Nolicx/Voron-Trident/Diagrams/Pins/SB2209 RP2040 Pinout.png

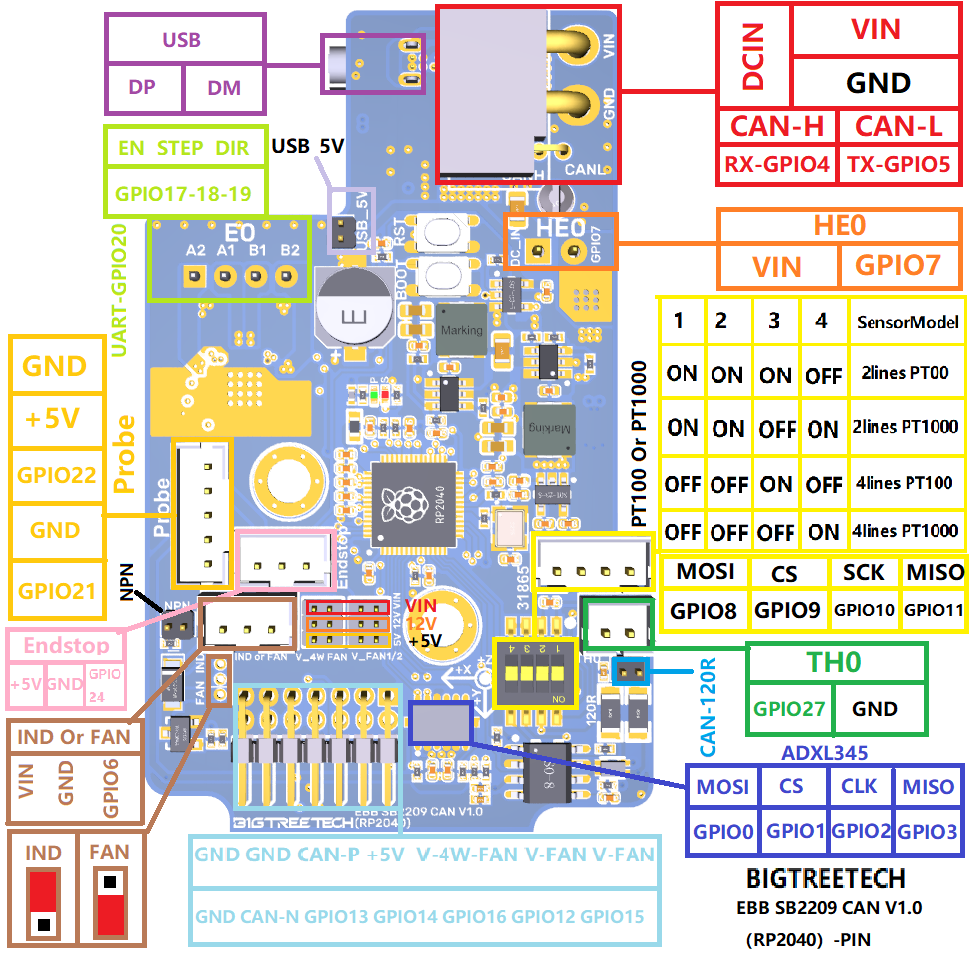
Diagrams/Pins/SB2209 RP2040 Pinout.png
