Nolicx/Voron-Trident/STL/ElectronicsBay/DIN_frame_mount_x4.stl

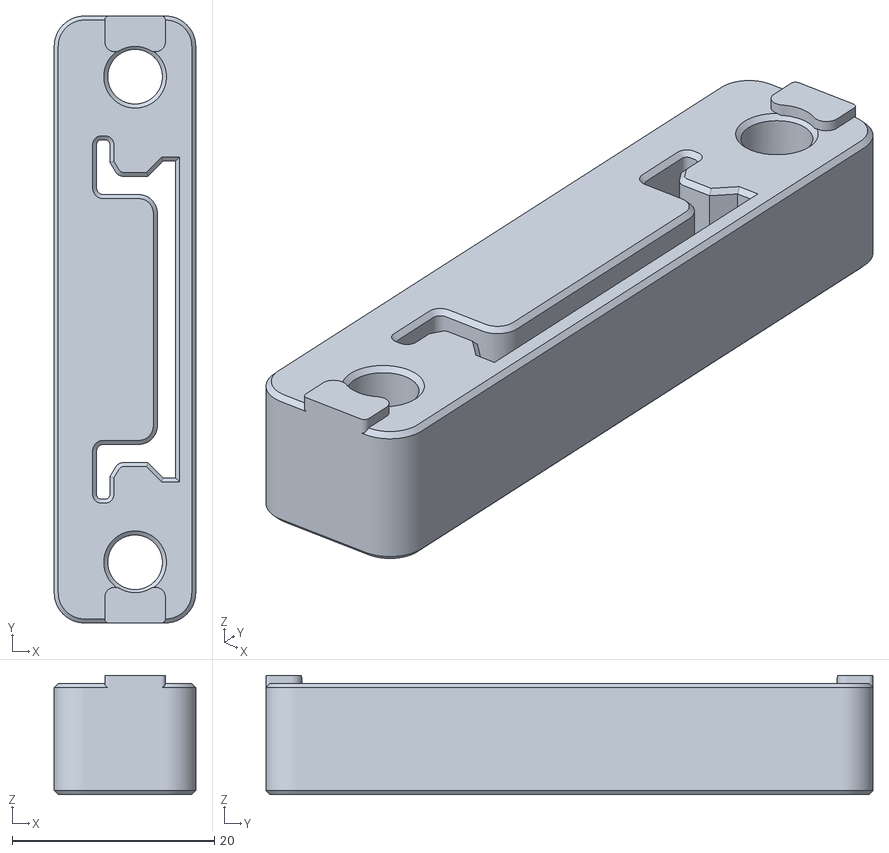
[picture p17: CAD file, 2025-08-13]
STL/ElectronicsBay/DIN_frame_mount_x4.stl
14.0 x 60.0 x 11.8
