Nolicx/Voron-Trident/STL/Exhaust_Filter/exhaust_filter_housing.stl

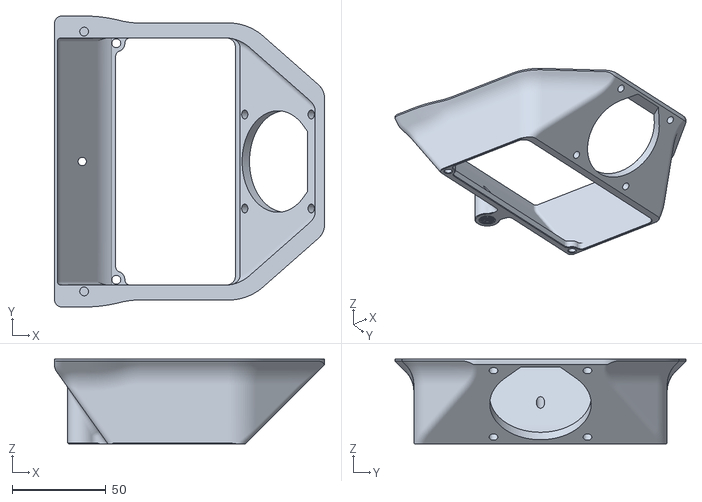
[picture p18: CAD file, 2025-08-13]
STL/Exhaust_Filter/exhaust_filter_housing.stl
143.7 x 154.8 x 45.0
