Nolicx/Voron-Trident/STL/Gantry/AB_Drive_Units/[a]_y_endstop_housing.stl

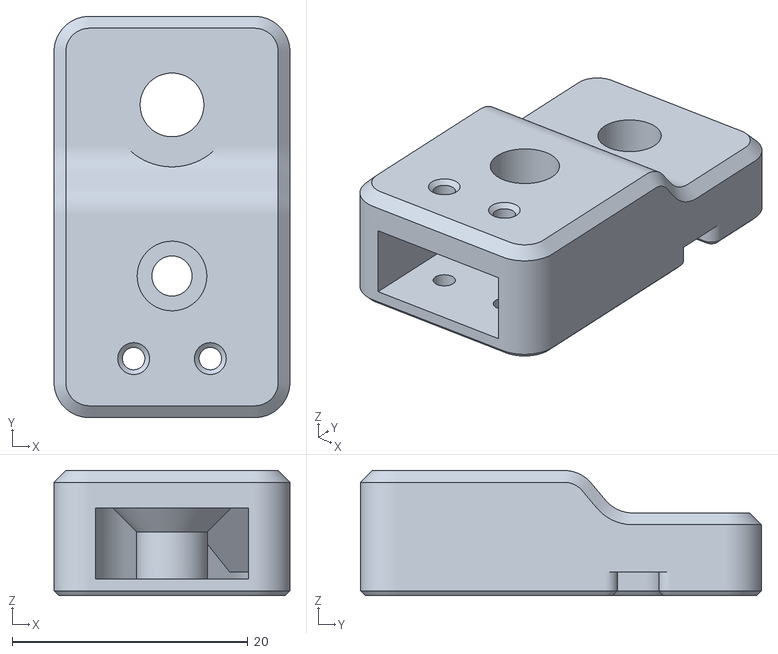
[picture p19: CAD file, 2025-08-13]
STL/Gantry/AB_Drive_Units/[a]_y_endstop_housing.stl
20.0 x 34.0 x 10.6
