Nolicx/Voron-Trident/STL/Gantry/PG7 Gantry Adapter.stl

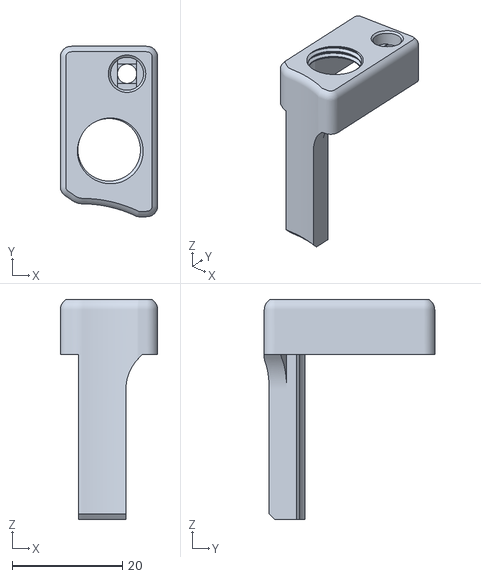
[picture p21: CAD file, 2025-08-13]
STL/Gantry/PG7 Gantry Adapter.stl
17.7 x 31.0 x 40.0
