Nolicx/Voron-Trident/STL/Gantry/XY_Joints/[a]_endstop_pod_hall_effect.stl

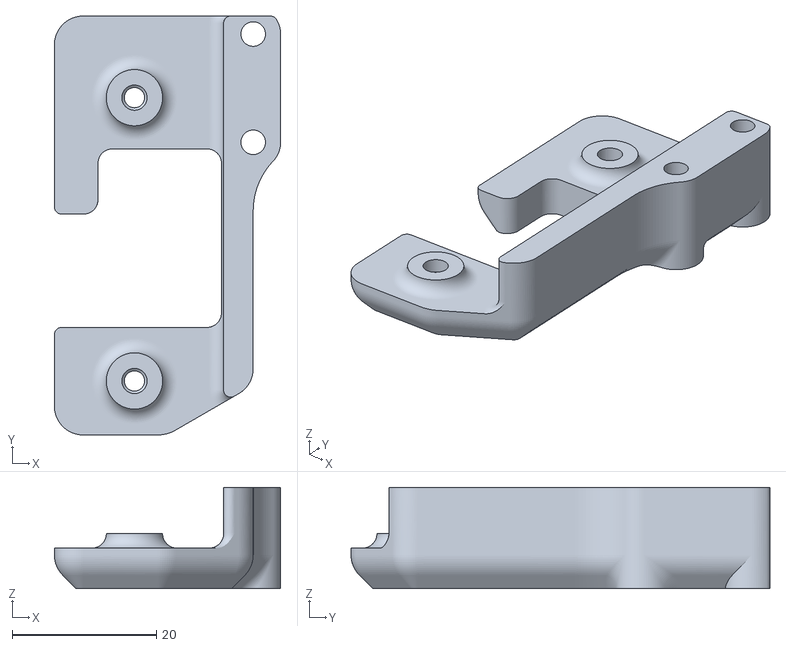
[picture p22: CAD file, 2025-08-13]
STL/Gantry/XY_Joints/[a]_endstop_pod_hall_effect.stl
31.4 x 58.0 x 14.0
