Nolicx/Voron-Trident/STL/Panels/bottom_panel_hinge_x2.stl

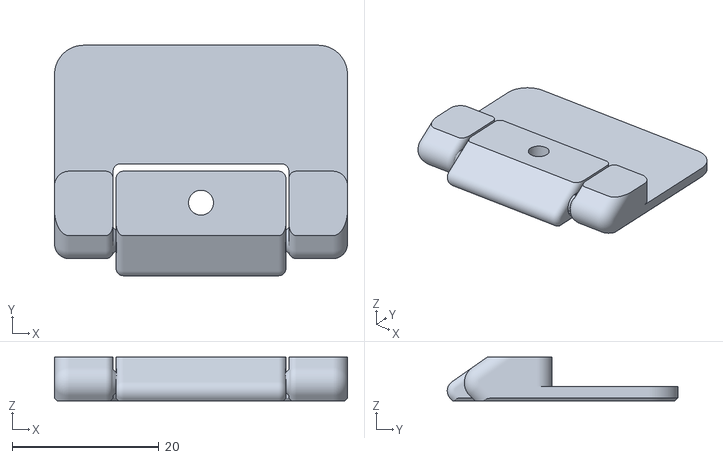
[picture p23: CAD file, 2025-08-13]
STL/Panels/bottom_panel_hinge_x2.stl
40.0 x 31.5 x 6.00
