Nolicx/Voron-Trident/STL/Panels/Front_Doors/handle_a_x2.stl

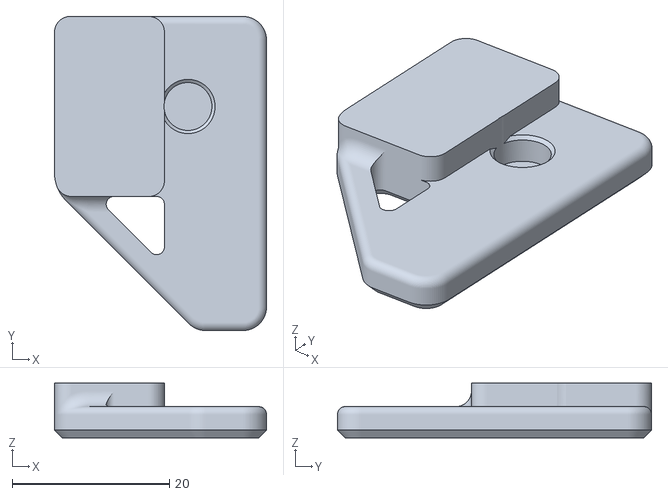
[picture p24: CAD file, 2025-08-13]
STL/Panels/Front_Doors/handle_a_x2.stl
27.0 x 40.0 x 7.00
