Nolicx/Voron-Trident/STL/Skirt/250/front_skirt_a_250.stl

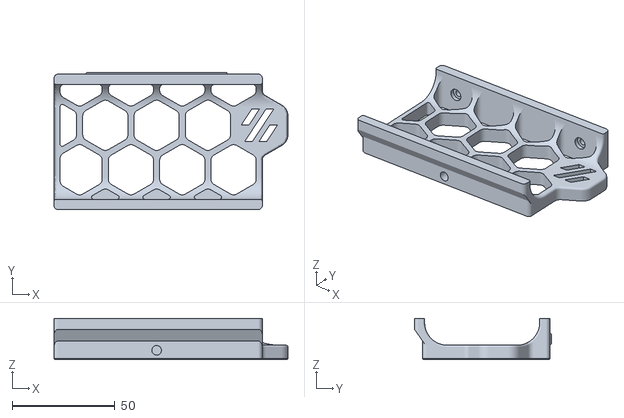
[picture p25: CAD file, 2025-08-13]
STL/Skirt/250/front_skirt_a_250.stl
114.0 x 66.8 x 20.0
