Nolicx/Voron-Trident/STL/Skirt/300/side_skirt_b_300_x2.stl

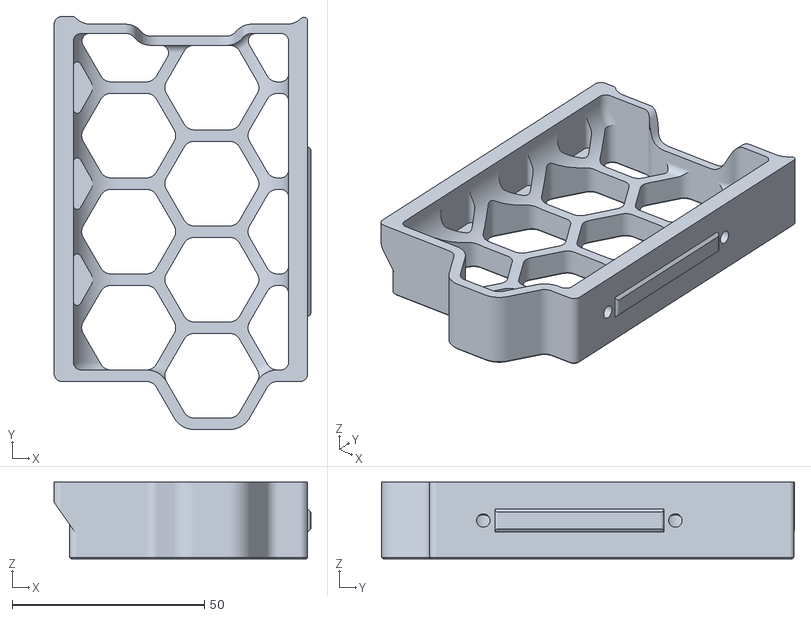
[picture p26: CAD file, 2025-08-13]
STL/Skirt/300/side_skirt_b_300_x2.stl
66.8 x 107.5 x 20.0
