Nolicx/Voron-Trident/STL/Skirt/350/front_skirt_a_350.stl

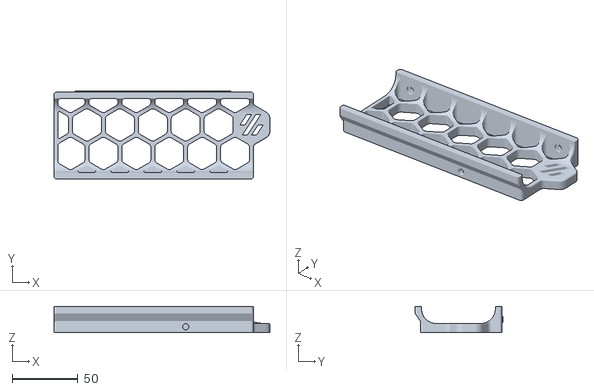
[picture p27: CAD file, 2025-08-13]
STL/Skirt/350/front_skirt_a_350.stl
164.0 x 66.8 x 20.0
