Nolicx/Voron-Trident/STL/Skirt/keystone_panel.stl

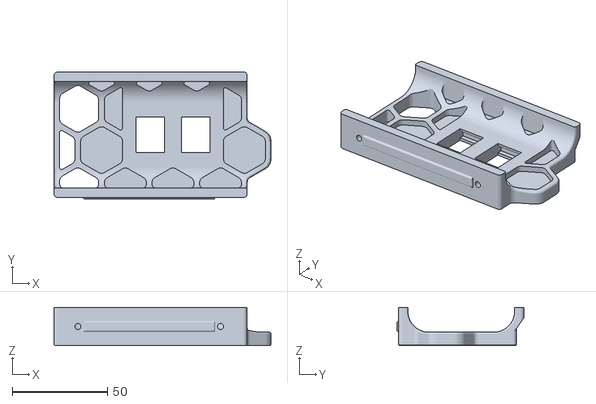
[picture p28: CAD file, 2025-08-13]
STL/Skirt/keystone_panel.stl
114.0 x 66.8 x 20.0
