Nolicx/Voron-Trident/STL/Spool_Management/bowden_retainer.stl

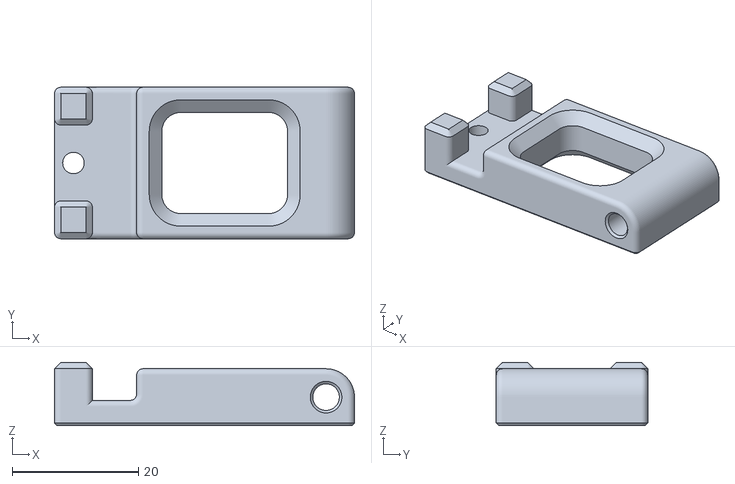
[picture p29: CAD file, 2025-08-13]
STL/Spool_Management/bowden_retainer.stl
47.5 x 24.0 x 10.00
