Nolicx/Voron-Trident/STL/Stealthburner/Clockwork2/[a]_anchor_pg7.stl

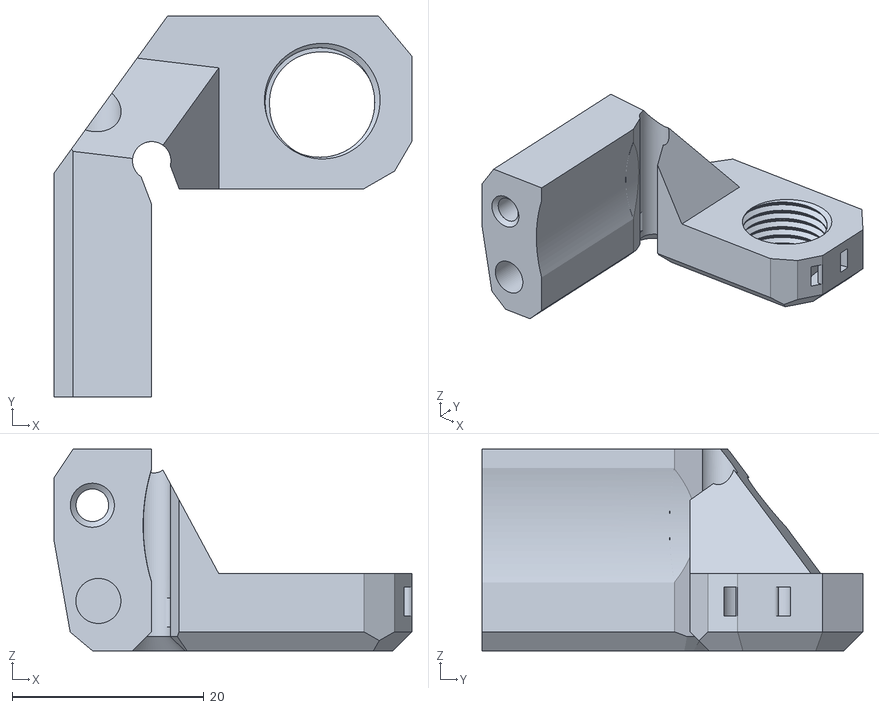
[picture p30: CAD file, 2025-08-13]
STL/Stealthburner/Clockwork2/[a]_anchor_pg7.stl
37.3 x 39.7 x 21.1
