Nolicx/Voron-Trident/STL/Stealthburner/Clockwork2/Direct_Drive/[a]_guidler_b.stl

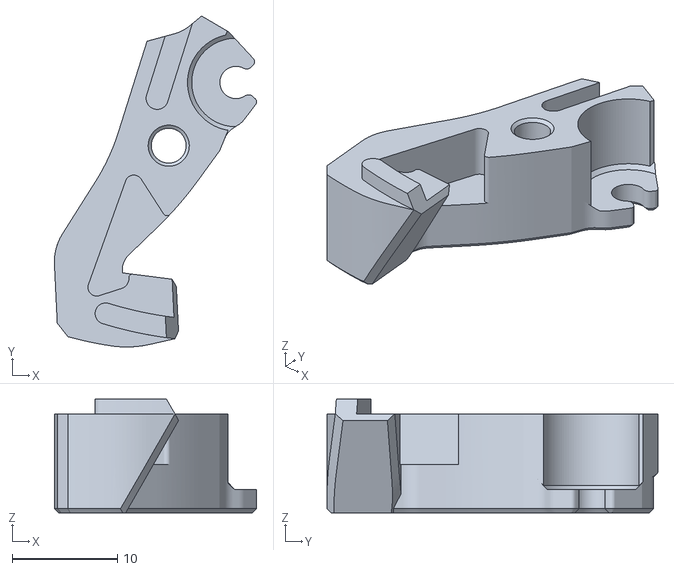
[picture p31: CAD file, 2025-08-13]
STL/Stealthburner/Clockwork2/Direct_Drive/[a]_guidler_b.stl
19.2 x 31.4 x 10.8
