Nolicx/Voron-Trident/STL/Stealthburner/Stealthburner/stealthburner_printhead_dragon_rear_cw2.stl

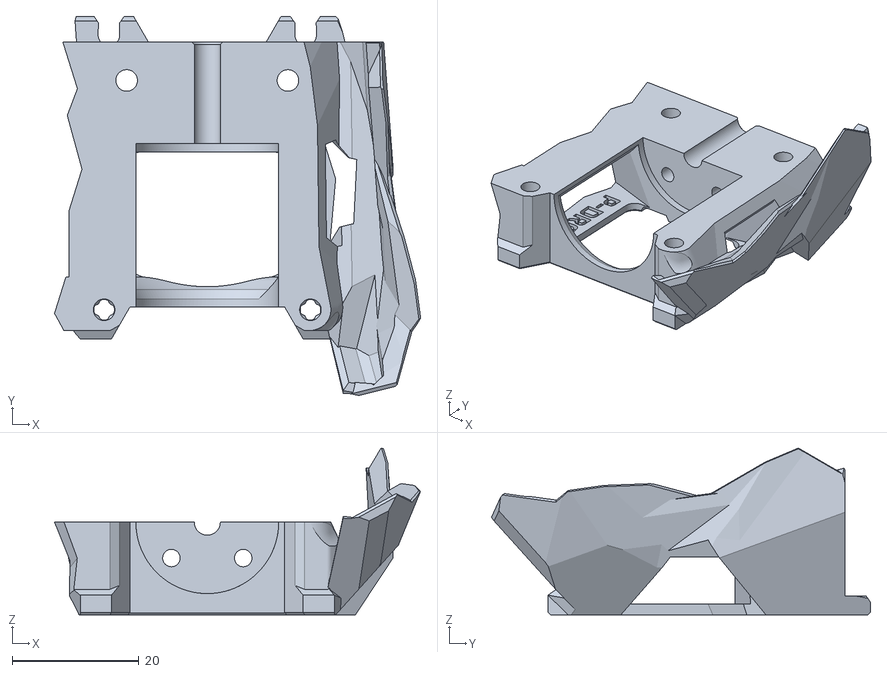
[picture p32: CAD file, 2025-08-13]
STL/Stealthburner/Stealthburner/stealthburner_printhead_dragon_rear_cw2.stl
57.7 x 59.7 x 26.3
