Nolicx/Voron-Trident/STL/Stealthburner/Tools/SB_5015_Cutting_Tool_B.stl

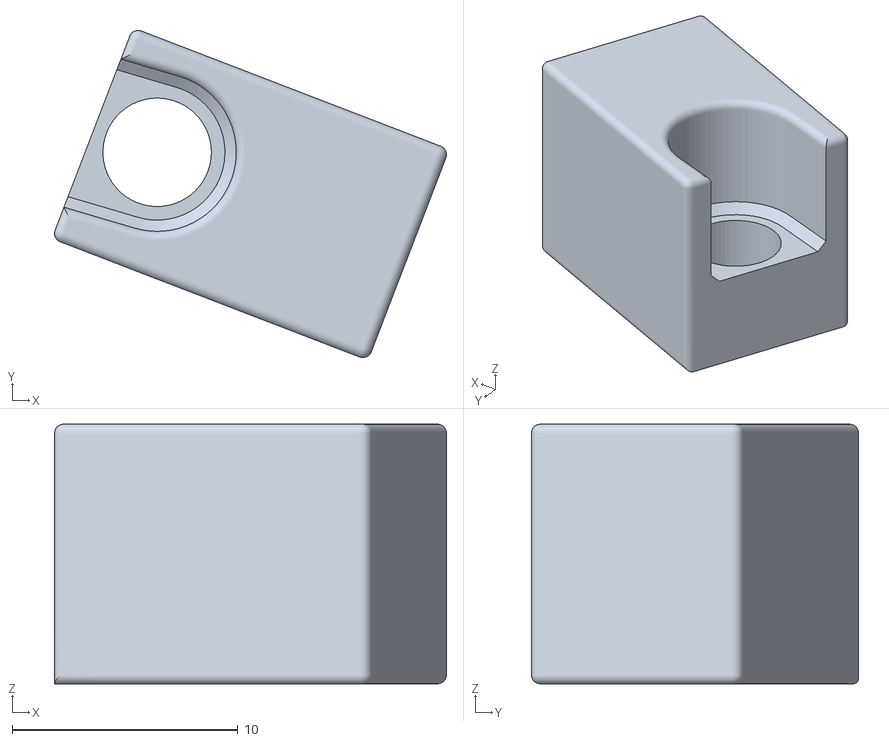
[picture p33: CAD file, 2025-08-13]
STL/Stealthburner/Tools/SB_5015_Cutting_Tool_B.stl
17.4 x 14.5 x 11.5
