Nolicx/Voron-Trident/STL/Tap/Tap_Upper_PCB_r8.stl

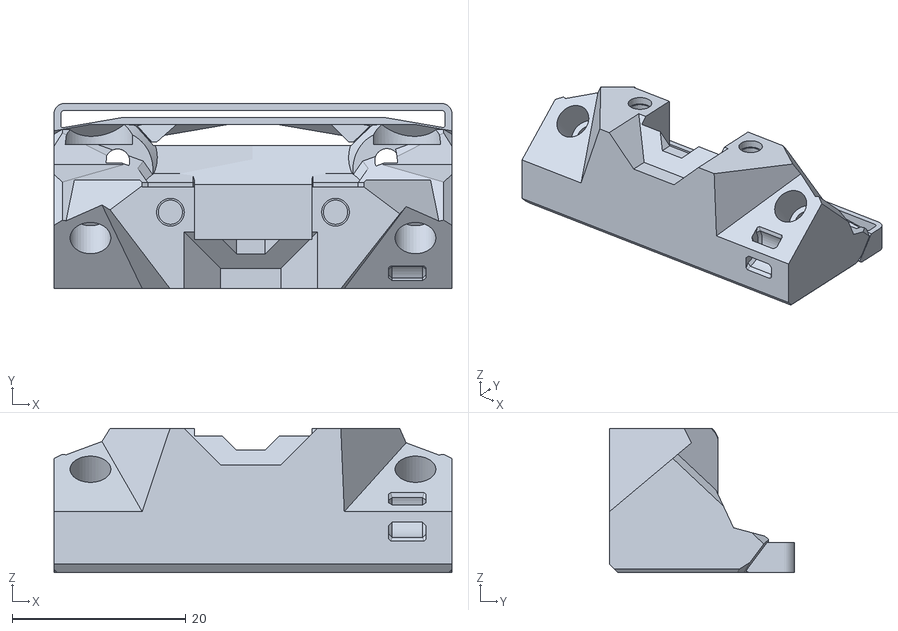
[picture p34: CAD file, 2025-08-13]
STL/Tap/Tap_Upper_PCB_r8.stl
45.8 x 21.3 x 16.6
