Nolicx/Voron-Trident/STL/Tools/pulley_jig.stl

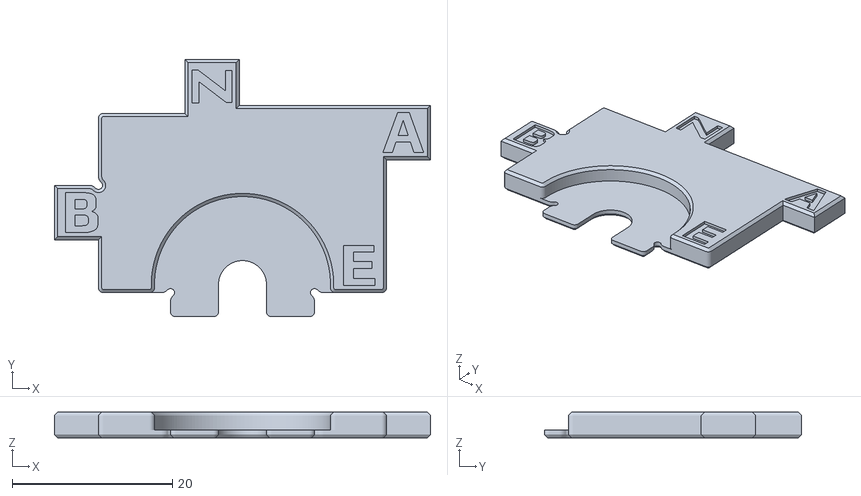
[picture p35: CAD file, 2025-08-13]
STL/Tools/pulley_jig.stl
47.0 x 32.2 x 3.20
