Nolicx/Voron-Trident/STL/Z_Assembly/z_rear_extrusionbracket_right.stl

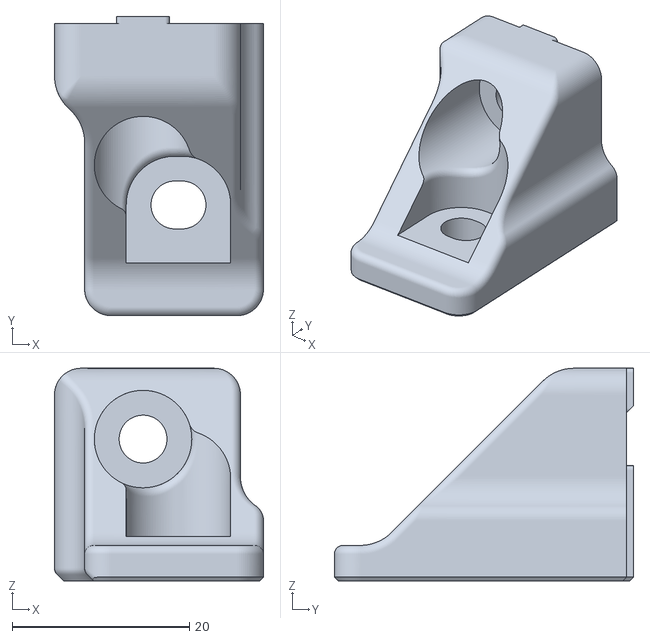
[picture p36: CAD file, 2025-08-13]
STL/Z_Assembly/z_rear_extrusionbracket_right.stl
23.6 x 33.8 x 24.0
