Nolicx/Voron-Trident/Mods/build_plate_stopper/Flex+Plate+Stops.stl

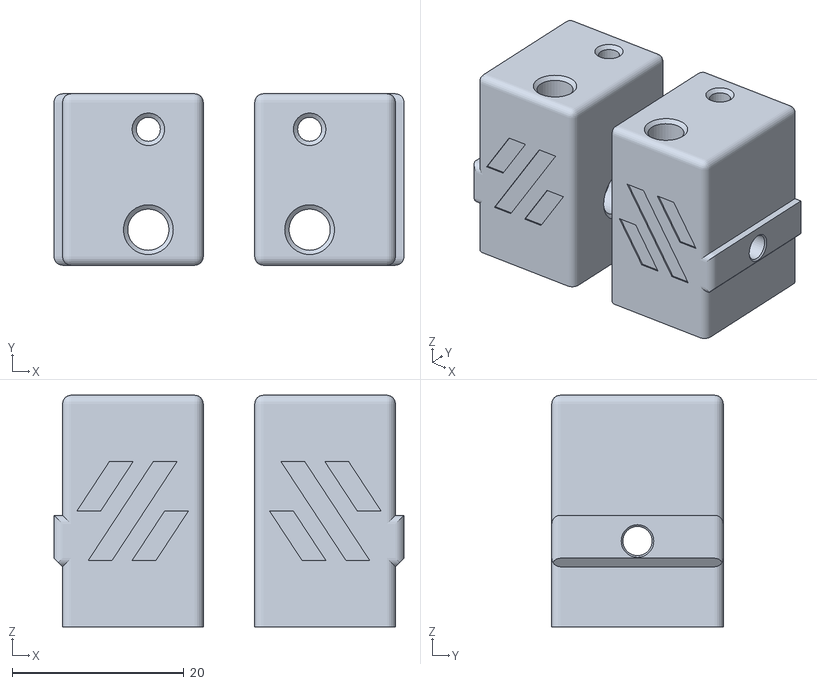
[picture p37: CAD file, 2026-03-26]
Mods/build_plate_stopper/Flex+Plate+Stops.stl
40.8 x 20.0 x 27.0
