Nolicx/Voron-Trident/Mods/spool_holders/Trident Internal Spool Holder rev2.0.stl

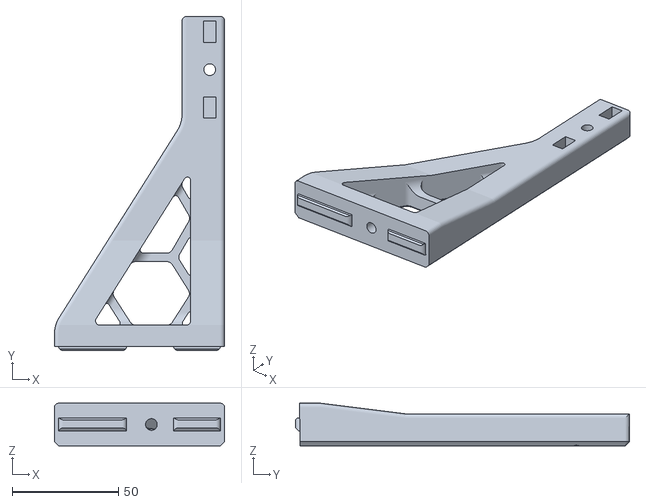
[picture p39: CAD file, 2026-03-26]
Mods/spool_holders/Trident Internal Spool Holder rev2.0.stl
80.0 x 156.9 x 20.0
