Nolicx/Voron-Trident/Mods/wago_mounts/Wago 221-413 3-Way Mount (x2).stl

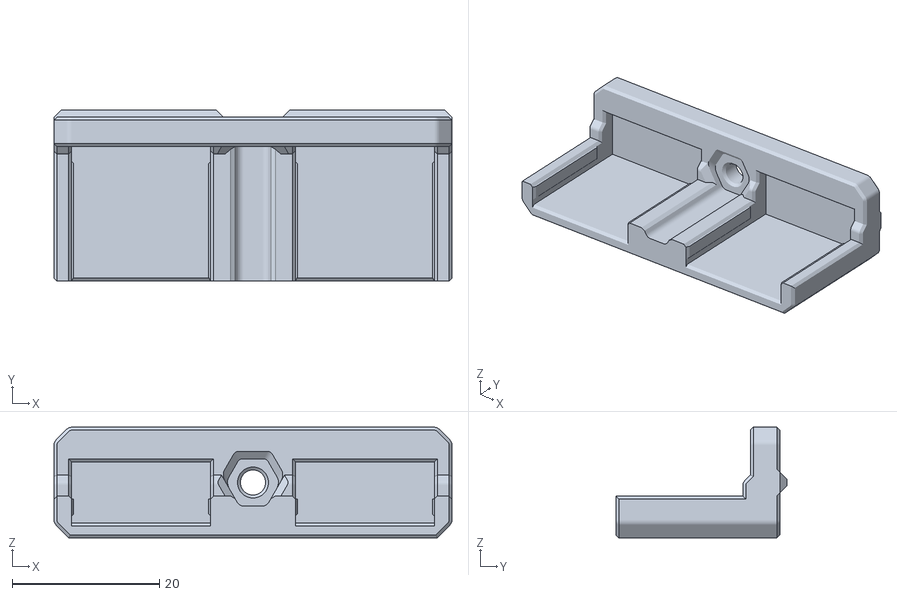
[picture p40: CAD file, 2026-05-21]
Mods/wago_mounts/Wago 221-413 3-Way Mount (x2).stl
54.0 x 23.2 x 15.0
