Nolicx/Voron-Trident/only custom STLs/Primary/cable support rod for CAN.STL

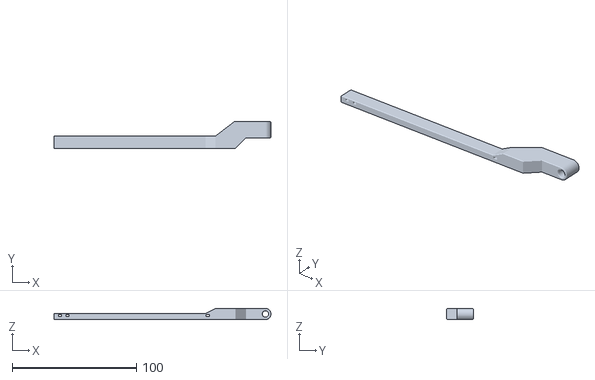
[picture p41: CAD file, 2025-08-13]
only custom STLs/Primary/cable support rod for CAN.STL
174.5 x 21.5 x 9.00
