Nolicx/Voron-Trident/only custom STLs/Primary/Nevermore/trident_bed_mount_bracket_right_r1.stl

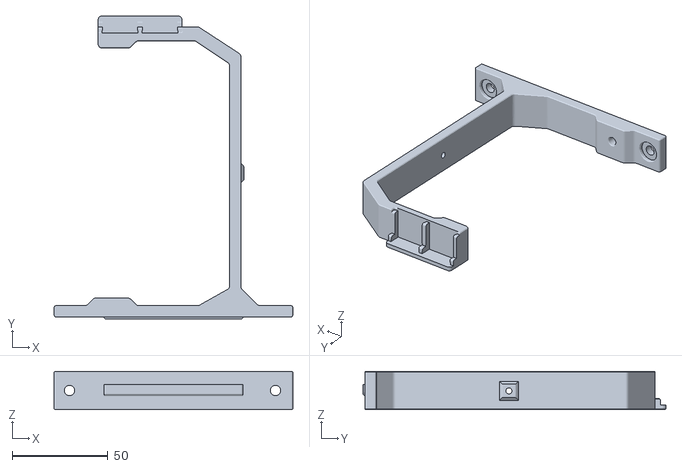
[picture p42: CAD file, 2025-08-13]
only custom STLs/Primary/Nevermore/trident_bed_mount_bracket_right_r1.stl
124.4 x 157.9 x 20.0
