Nolicx/Voron-Trident/STL/ElectronicsBay/lrs_psu_bracket_x2.stl

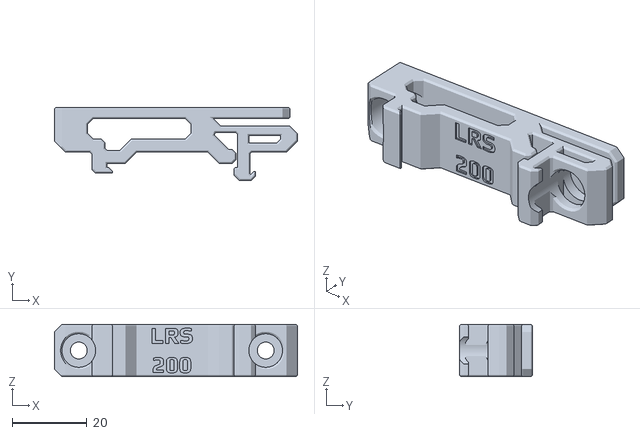
[picture p43: CAD file, 2025-08-13]
STL/ElectronicsBay/lrs_psu_bracket_x2.stl
65.0 x 19.6 x 14.0
