Nolicx/Voron-Trident/STL/Exhaust_Filter/exhaust_filter_grill.stl

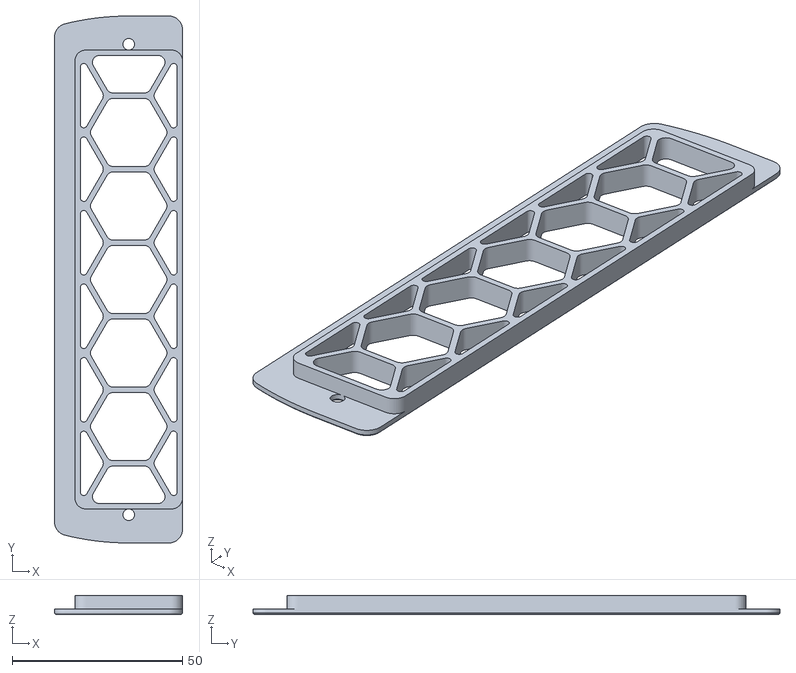
[picture p44: CAD file, 2025-08-13]
STL/Exhaust_Filter/exhaust_filter_grill.stl
37.6 x 154.8 x 5.60
