Nolicx/Voron-Trident/STL/Gantry/AB_Drive_Units/[a]_y_endstop_bumper.stl

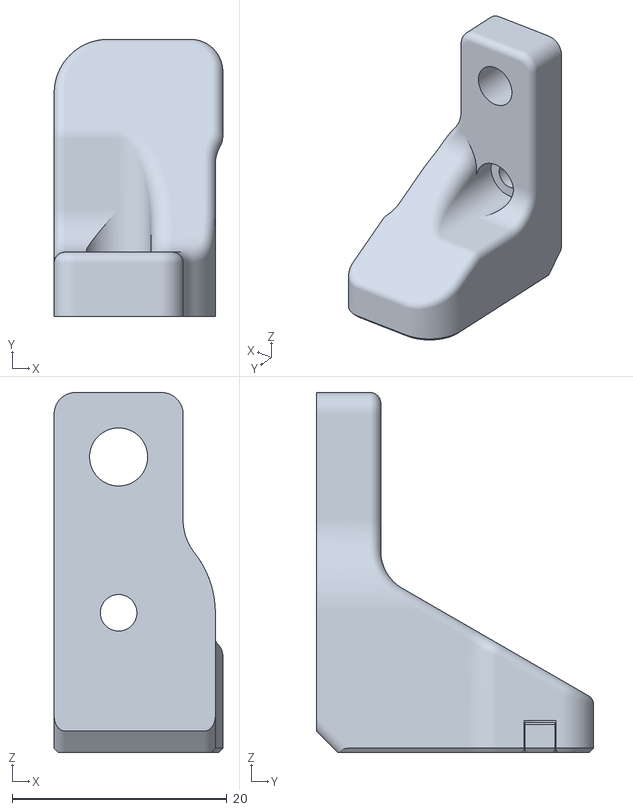
[picture p45: CAD file, 2025-08-13]
STL/Gantry/AB_Drive_Units/[a]_y_endstop_bumper.stl
15.7 x 25.8 x 33.5
