Nolicx/Voron-Trident/STL/Gantry/chain_wire_anchor_a_3hole.stl

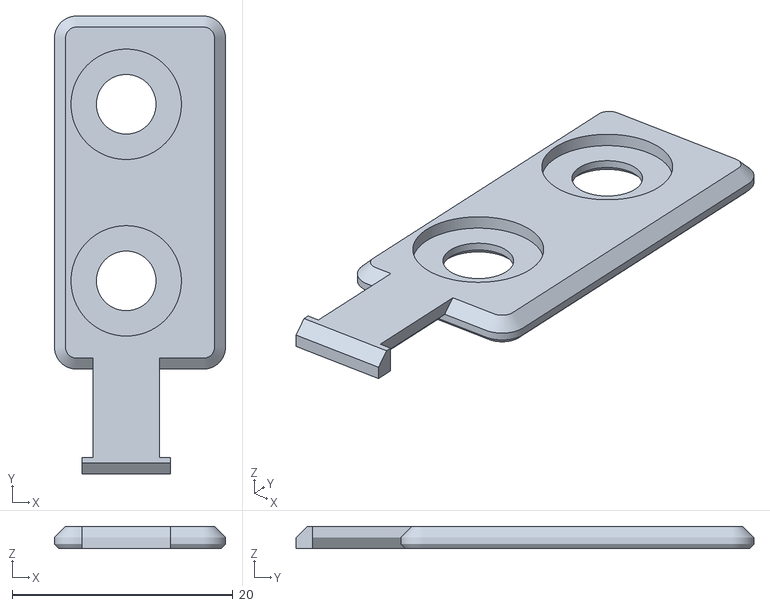
[picture p46: CAD file, 2025-08-13]
STL/Gantry/chain_wire_anchor_a_3hole.stl
15.5 x 41.5 x 2.00
