Nolicx/Voron-Trident/STL/Gantry/Front_Idlers/[a]_tensioner_left.stl

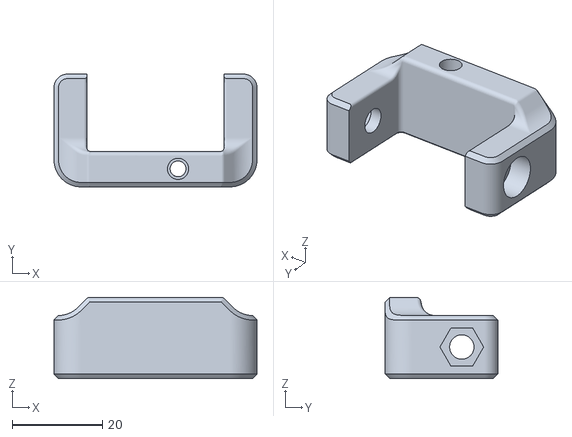
[picture p47: CAD file, 2025-08-13]
STL/Gantry/Front_Idlers/[a]_tensioner_left.stl
45.0 x 25.0 x 18.0
