Nolicx/Voron-Trident/STL/Gantry/XY_Joints/xy_joint_left_upper_MGN12.stl

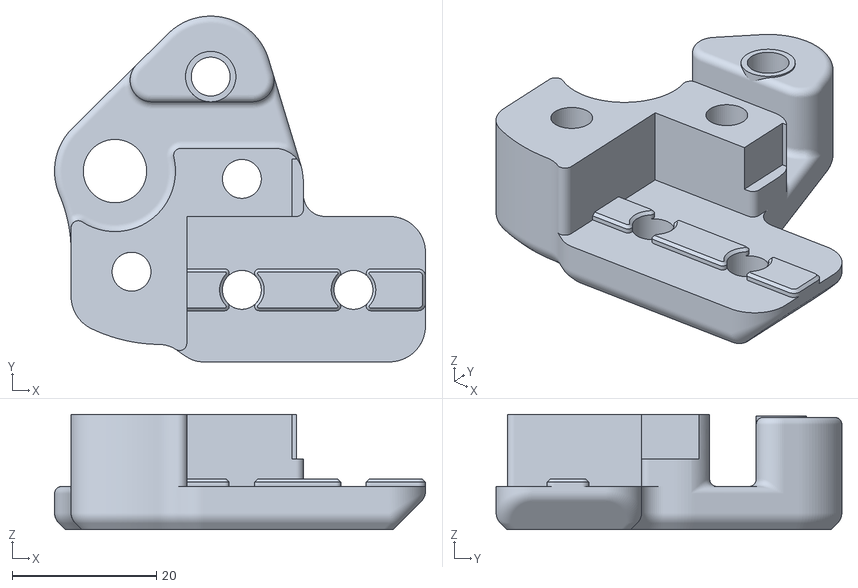
[picture p48: CAD file, 2025-08-13]
STL/Gantry/XY_Joints/xy_joint_left_upper_MGN12.stl
51.5 x 48.0 x 16.0
