Nolicx/Voron-Trident/STL/Nevermore/Trident_Bed_Mount_XL_Cartridge_LID.stl

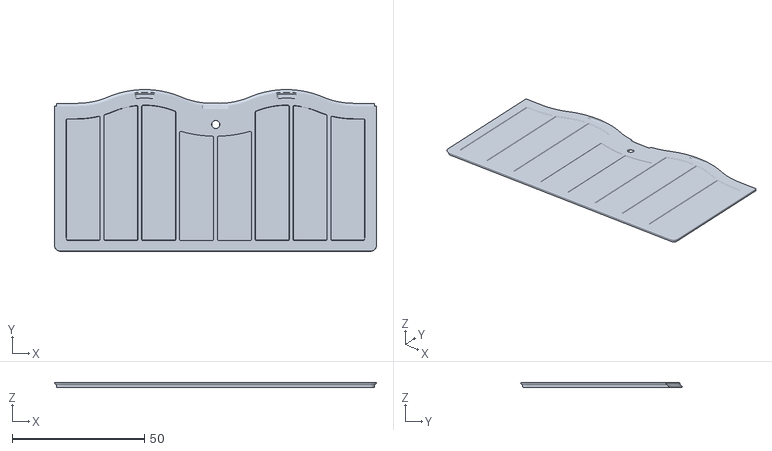
[picture p49: CAD file, 2025-08-13]
STL/Nevermore/Trident_Bed_Mount_XL_Cartridge_LID.stl
122.0 x 61.3 x 1.78
