Nolicx/Voron-Trident/STL/Panels/wire_cover_right.stl

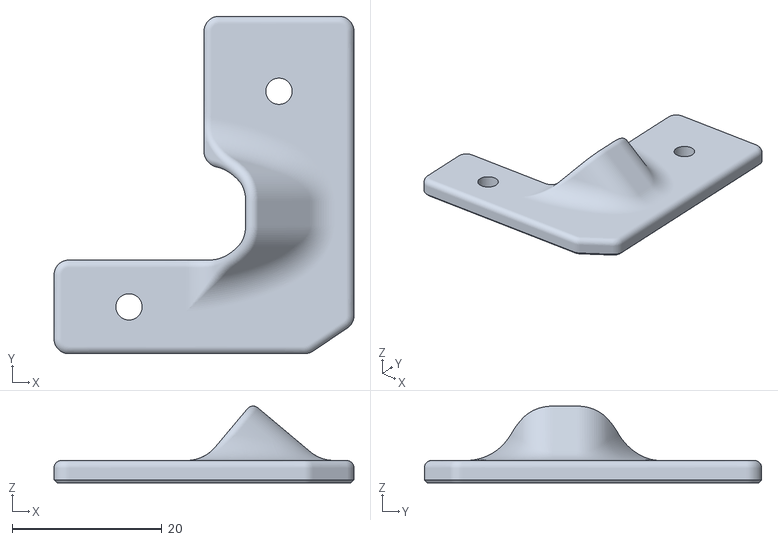
[picture p50: CAD file, 2025-08-13]
STL/Panels/wire_cover_right.stl
40.0 x 45.0 x 10.3
