Nolicx/Voron-Trident/STL/Skirt/250/side_skirt_a_250_x2.stl

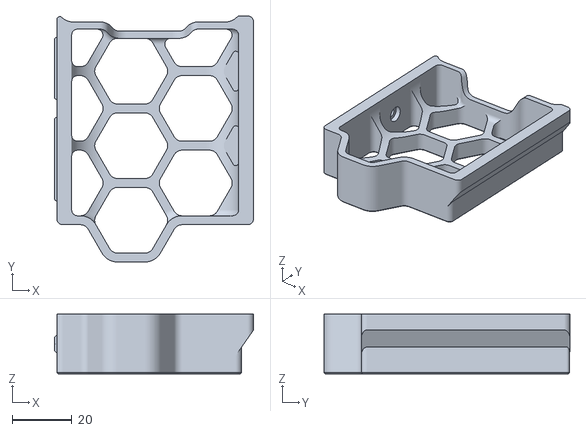
[picture p51: CAD file, 2025-08-13]
STL/Skirt/250/side_skirt_a_250_x2.stl
66.8 x 82.5 x 20.0
