Nolicx/Voron-Trident/STL/Skirt/300/rear_center_skirt_300.stl

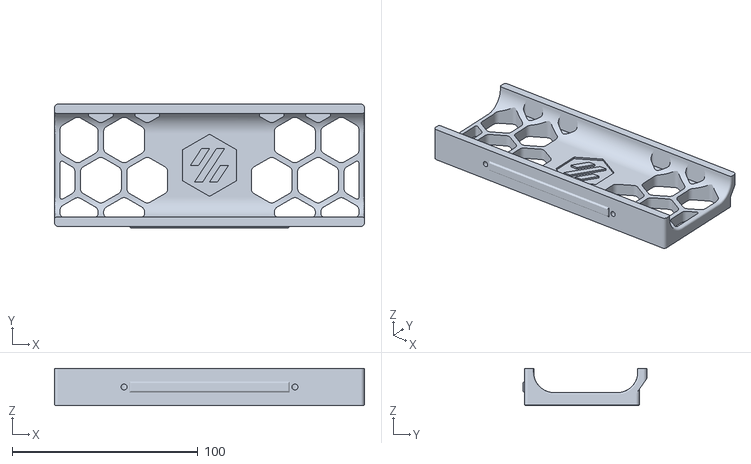
[picture p52: CAD file, 2025-08-13]
STL/Skirt/300/rear_center_skirt_300.stl
167.0 x 66.8 x 20.0
