Nolicx/Voron-Trident/STL/Skirt/[a]_fan_grill_a_x2.stl

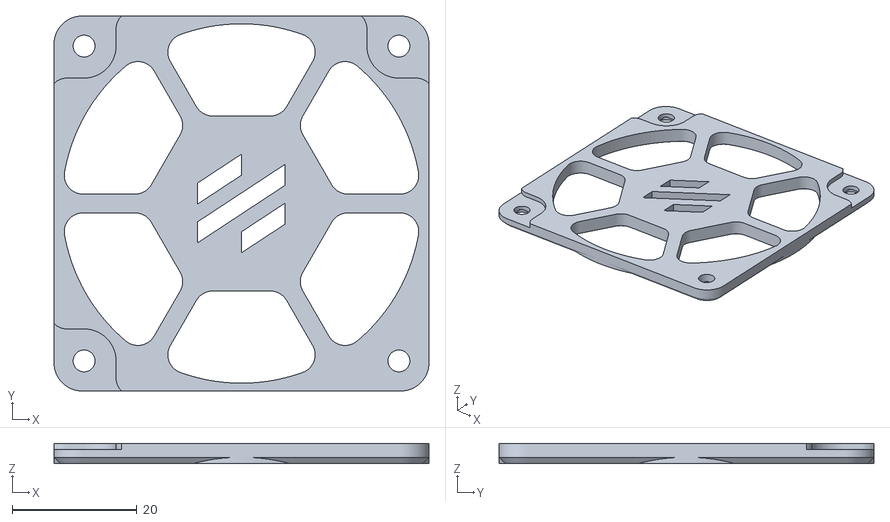
[picture p53: CAD file, 2025-08-13]
STL/Skirt/[a]_fan_grill_a_x2.stl
60.0 x 60.0 x 3.20
