Nolicx/Voron-Trident/STL/Spool_Management/spool_holder.stl

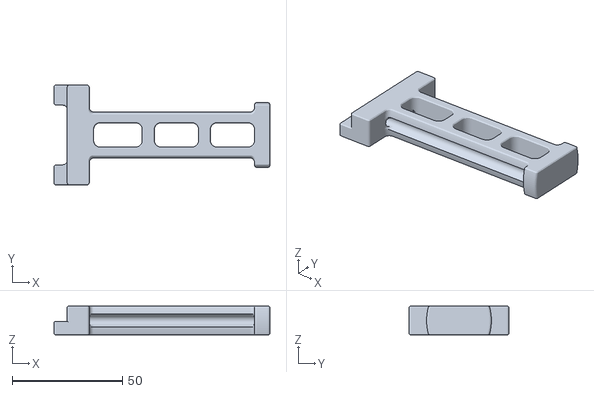
[picture p54: CAD file, 2025-08-13]
STL/Spool_Management/spool_holder.stl
98.0 x 45.4 x 13.0
