Nolicx/Voron-Trident/STL/Stealthburner/Clockwork2/[a]_pcb_spacer.stl

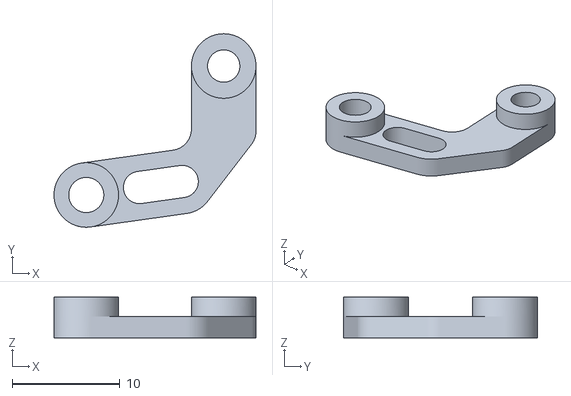
[picture p55: CAD file, 2025-08-13]
STL/Stealthburner/Clockwork2/[a]_pcb_spacer.stl
18.8 x 18.0 x 3.80
