Nolicx/Voron-Trident/STL/Stealthburner/Stealthburner/[o]_stealthburner_LED_carrier.stl

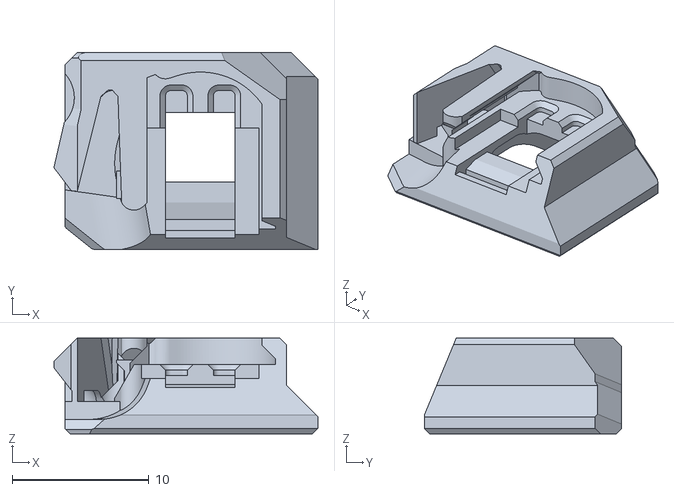
[picture p56: CAD file, 2025-08-13]
STL/Stealthburner/Stealthburner/[o]_stealthburner_LED_carrier.stl
19.3 x 14.4 x 7.01
