Nolicx/Voron-Trident/STL/Stealthburner/Tools/SB_5015_Cutting_Tool_A.stl

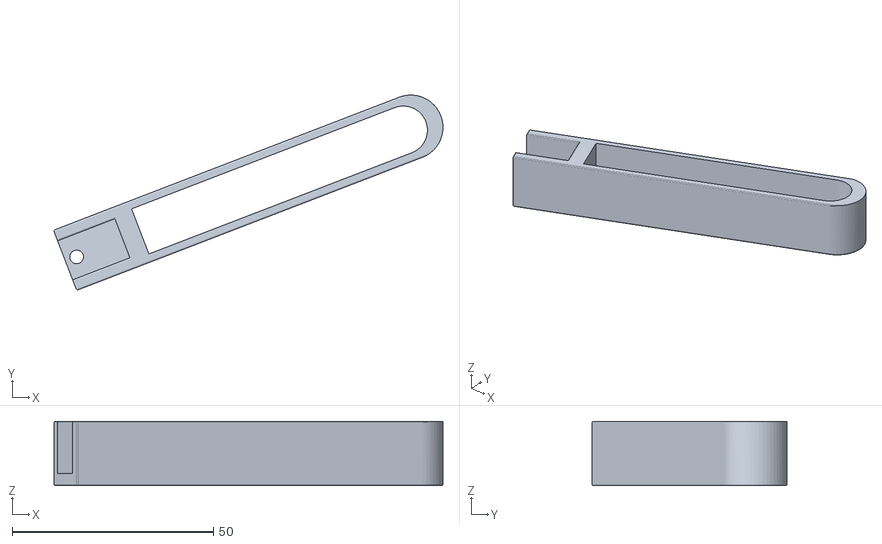
[picture p57: CAD file, 2025-08-13]
STL/Stealthburner/Tools/SB_5015_Cutting_Tool_A.stl
96.6 x 48.4 x 16.0
