Nolicx/Voron-Trident/STL/Tap/[a]_Tap_Belt_Cover_r8_x2.stl

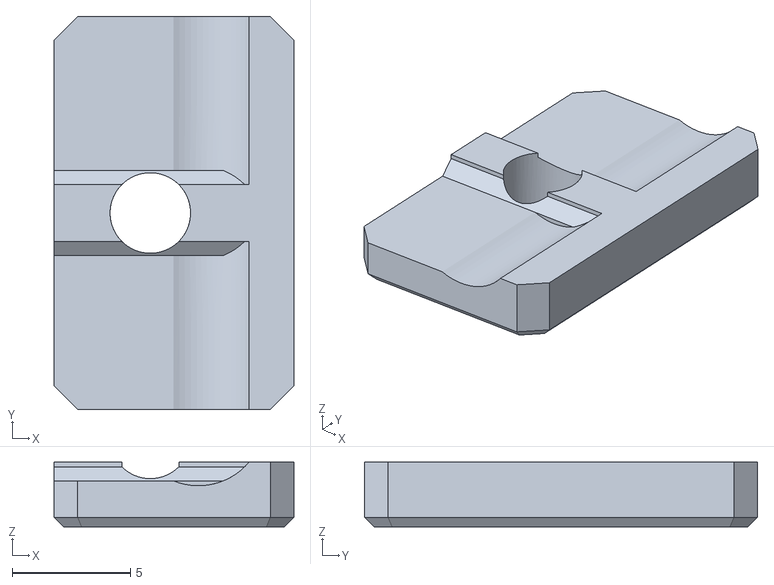
[picture p58: CAD file, 2025-08-13]
STL/Tap/[a]_Tap_Belt_Cover_r8_x2.stl
10.1 x 16.6 x 2.74
