Nolicx/Voron-Trident/STL/Tools/MGN12_rail_guide_x2.stl

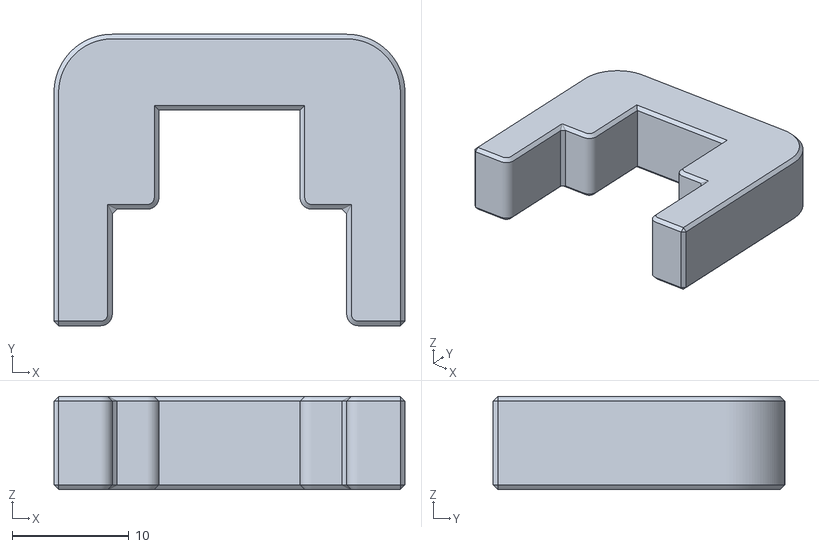
[picture p59: CAD file, 2025-08-13]
STL/Tools/MGN12_rail_guide_x2.stl
30.1 x 25.0 x 8.00
