Nolicx/Voron-Trident/STL/Z_Assembly/z_stepper_left.stl

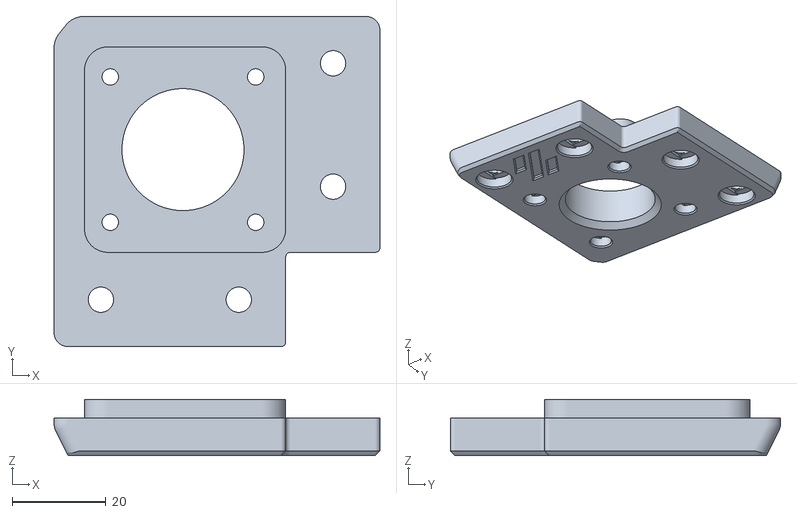
[picture p60: CAD file, 2025-08-13]
STL/Z_Assembly/z_stepper_left.stl
69.5 x 70.4 x 12.0
