Nolicx/Voron-Trident/Mods/ptfe_bowden_guide/voron-bowden-ptfe-tube-guide-arm-and-canbus-cable-support-model_files/STL's/short_arm.stl

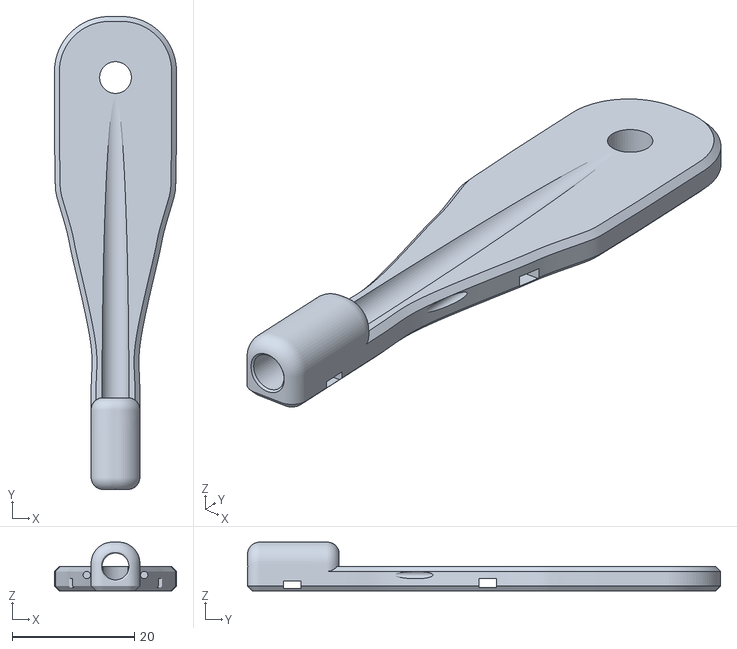
[picture p61: CAD file, 2026-05-21]
Mods/ptfe_bowden_guide/voron-bowden-ptfe-tube-guide-arm-and-canbus-cable-support-model_files/STL's/short_arm.stl
20.0 x 77.5 x 8.00
