Nolicx/Voron-Trident/Mods/spool_holders/Classic__spool_holder.stl

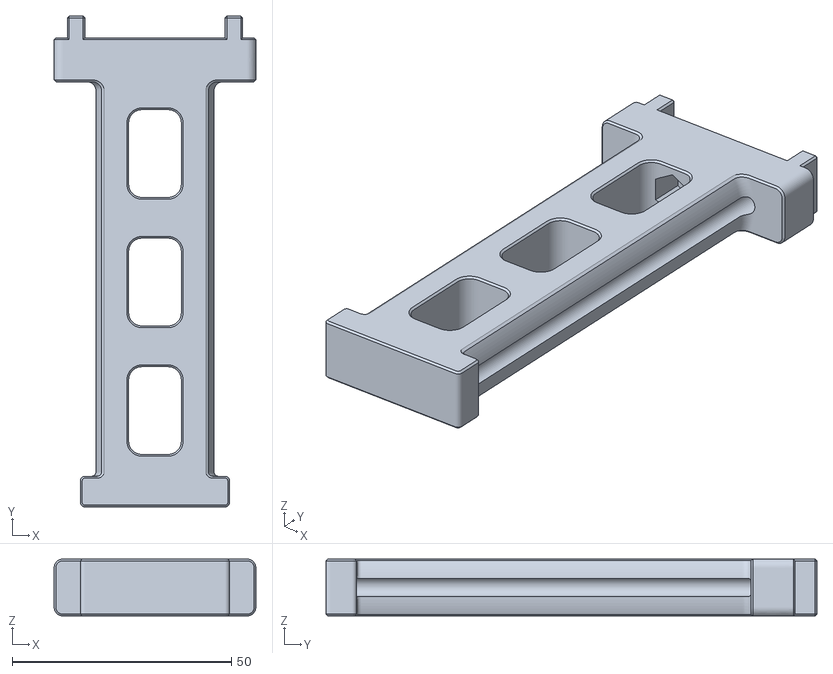
[picture p62: CAD file, 2026-03-26]
Mods/spool_holders/Classic__spool_holder.stl
46.0 x 112.0 x 13.0
