Nolicx/Voron-Trident/Mods/wago_mounts/large_wago.stl

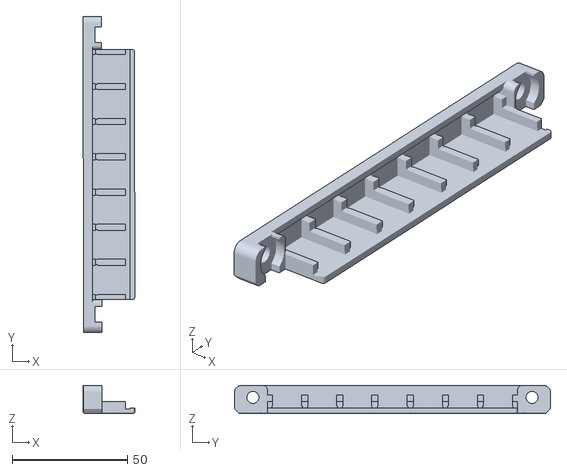
[picture p63: CAD file, 2026-05-21]
Mods/wago_mounts/large_wago.stl
22.4 x 137.0 x 12.2
