Nolicx/Voron-Trident/only custom STLs/Accent/BTT HDMI5 V1_2 mount frame_Regular.stl

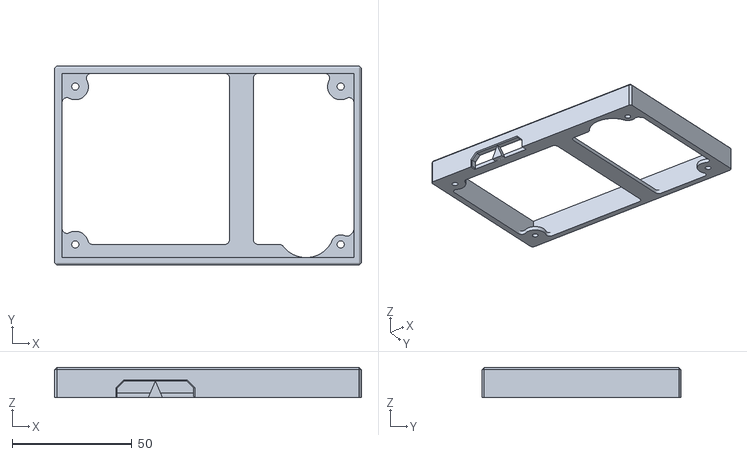
[picture p64: CAD file, 2025-08-13]
only custom STLs/Accent/BTT HDMI5 V1_2 mount frame_Regular.stl
128.4 x 83.4 x 12.7
