Nolicx/Voron-Trident/only custom STLs/Primary/Nevermore/Trident_Bed_Mount_Plenum.stl

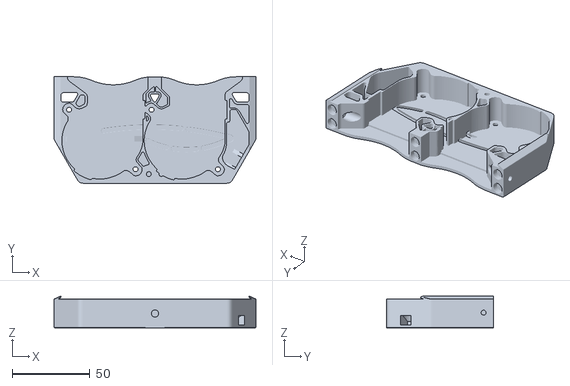
[picture p65: CAD file, 2025-08-13]
only custom STLs/Primary/Nevermore/Trident_Bed_Mount_Plenum.stl
130.0 x 68.6 x 20.5
