Nolicx/Voron-Trident/STL/ElectronicsBay/cable_frame_anchor_x6.stl

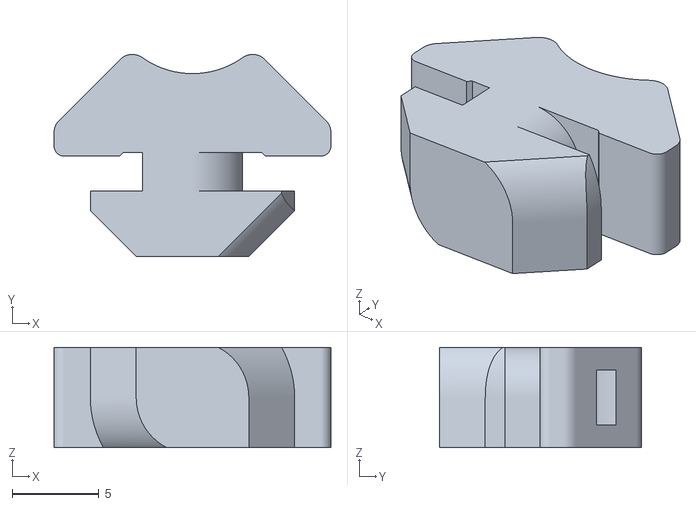
[picture p66: CAD file, 2025-08-13]
STL/ElectronicsBay/cable_frame_anchor_x6.stl
16.0 x 11.7 x 5.80
