Nolicx/Voron-Trident/STL/Exhaust_Filter/[a]_filter_access_cover.stl

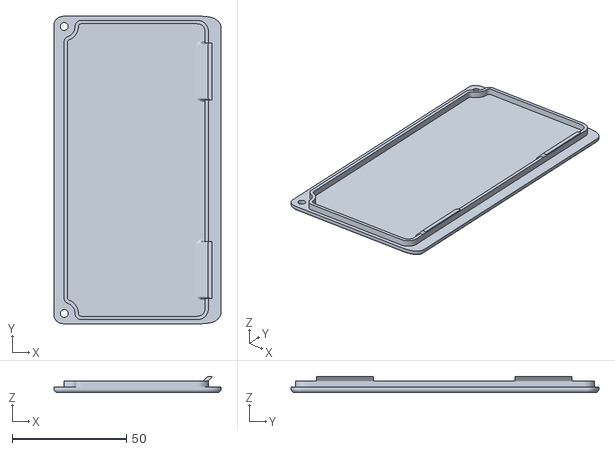
[picture p67: CAD file, 2025-08-13]
STL/Exhaust_Filter/[a]_filter_access_cover.stl
73.2 x 134.8 x 7.20
