Nolicx/Voron-Trident/STL/Gantry/AB_Drive_Units/[a]_wire_cover.stl

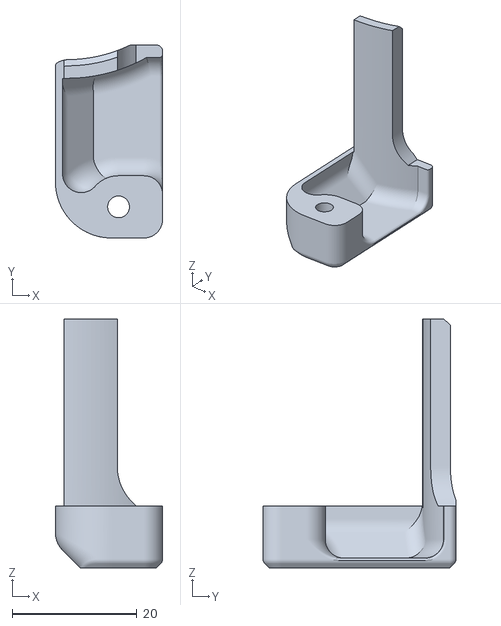
[picture p68: CAD file, 2025-08-13]
STL/Gantry/AB_Drive_Units/[a]_wire_cover.stl
17.2 x 31.0 x 40.0
