Nolicx/Voron-Trident/STL/Gantry/chain_wire_anchor_3hole_x2.stl

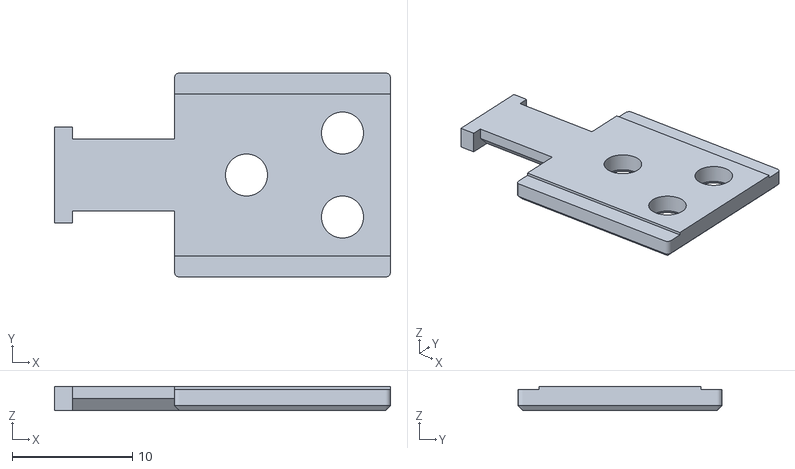
[picture p69: CAD file, 2025-08-13]
STL/Gantry/chain_wire_anchor_3hole_x2.stl
28.0 x 17.0 x 2.00
