Nolicx/Voron-Trident/STL/Gantry/XY_Joints/[a]_endstop_pod_D2F_switch.stl

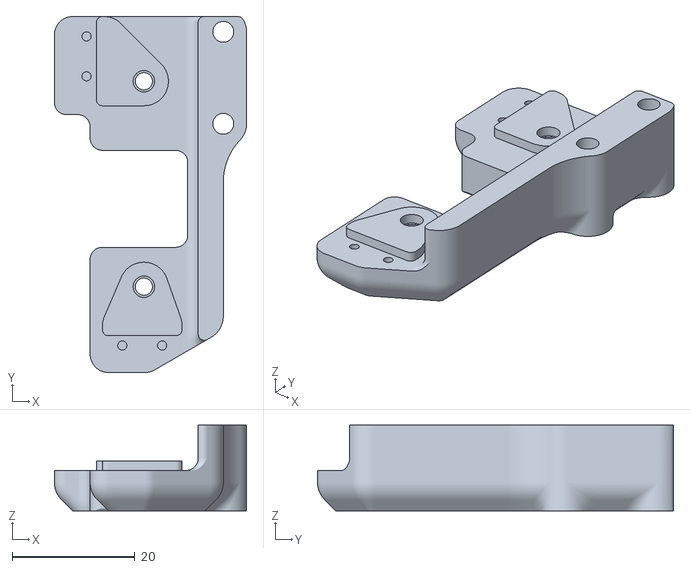
[picture p70: CAD file, 2025-08-13]
STL/Gantry/XY_Joints/[a]_endstop_pod_D2F_switch.stl
31.4 x 58.0 x 14.0
