Nolicx/Voron-Trident/STL/Panels/Front_Doors/door_hinge_x6.stl

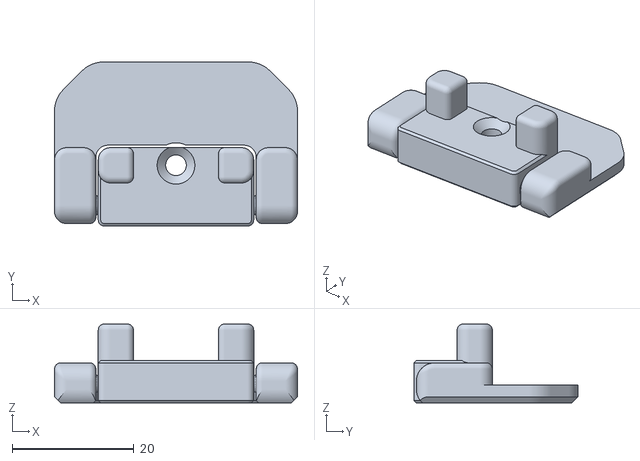
[picture p71: CAD file, 2025-08-13]
STL/Panels/Front_Doors/door_hinge_x6.stl
40.0 x 27.0 x 13.0
