Nolicx/Voron-Trident/STL/Skirt/300/front_skirt_b_300.stl

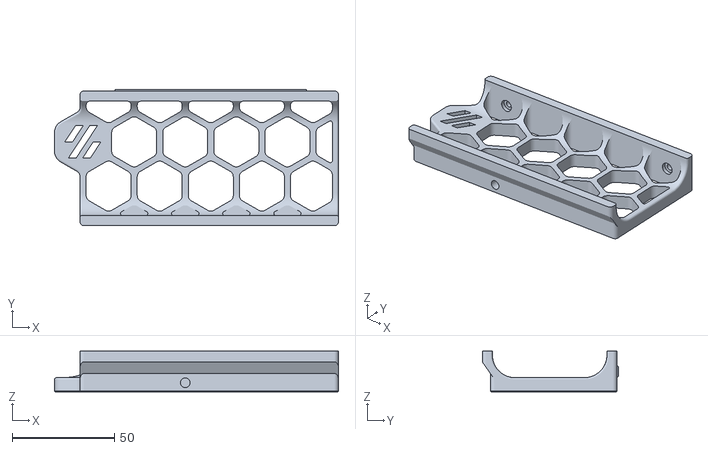
[picture p72: CAD file, 2025-08-13]
STL/Skirt/300/front_skirt_b_300.stl
139.0 x 66.8 x 20.0
