Nolicx/Voron-Trident/STL/Skirt/350/side_skirt_a_350_x2.stl

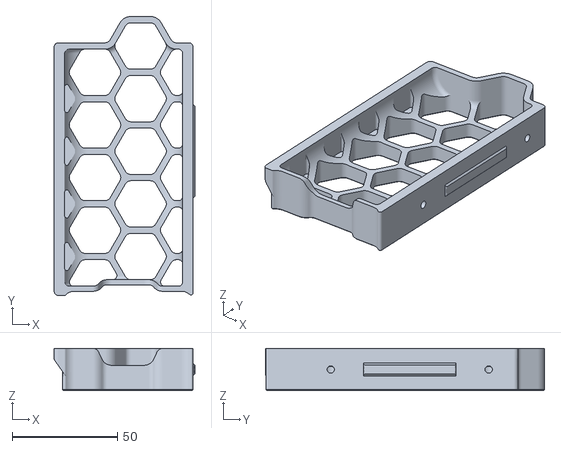
[picture p73: CAD file, 2025-08-13]
STL/Skirt/350/side_skirt_a_350_x2.stl
66.8 x 132.5 x 20.0
