Nolicx/Voron-Trident/STL/Skirt/[a]_keystone_blank_insert_x2.stl

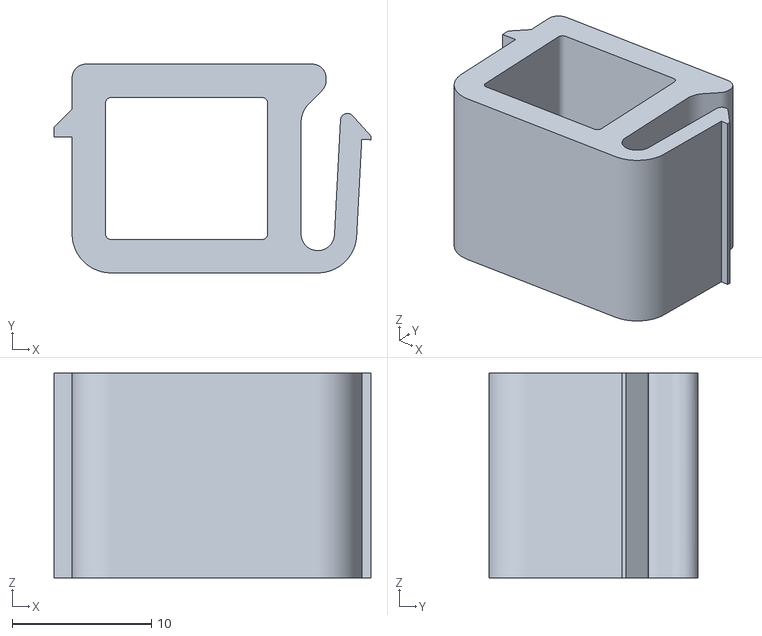
[picture p74: CAD file, 2025-08-13]
STL/Skirt/[a]_keystone_blank_insert_x2.stl
22.8 x 15.0 x 14.7
