Nolicx/Voron-Trident/STL/Stealthburner/Clockwork2/cable_door_for_pcb.stl

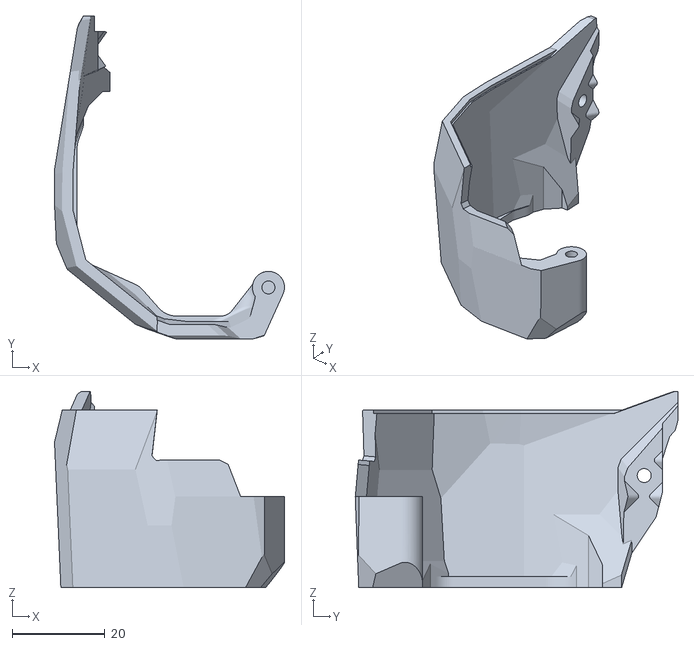
[picture p75: CAD file, 2025-08-13]
STL/Stealthburner/Clockwork2/cable_door_for_pcb.stl
49.5 x 69.4 x 42.2
