Nolicx/Voron-Trident/STL/Stealthburner/Clockwork2/Direct_Drive/[a]_latch_shuttle.stl

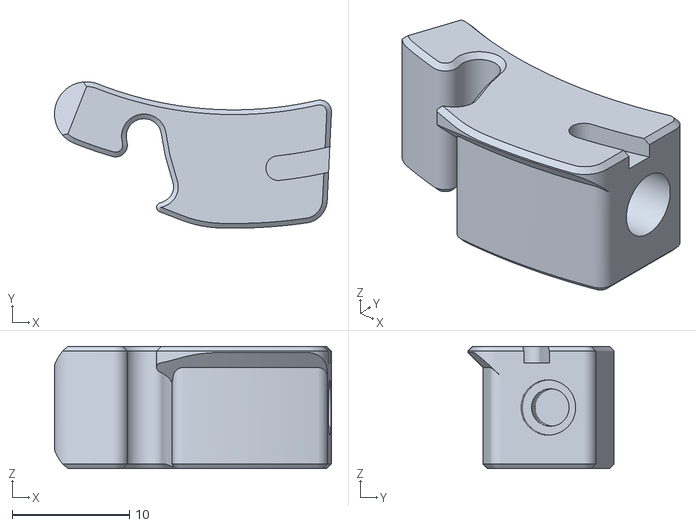
[picture p76: CAD file, 2025-08-13]
STL/Stealthburner/Clockwork2/Direct_Drive/[a]_latch_shuttle.stl
23.6 x 12.5 x 10.4
