Nolicx/Voron-Trident/STL/Stealthburner/Stealthburner/[o]_stealthburner_LED_diffuser_mask.stl

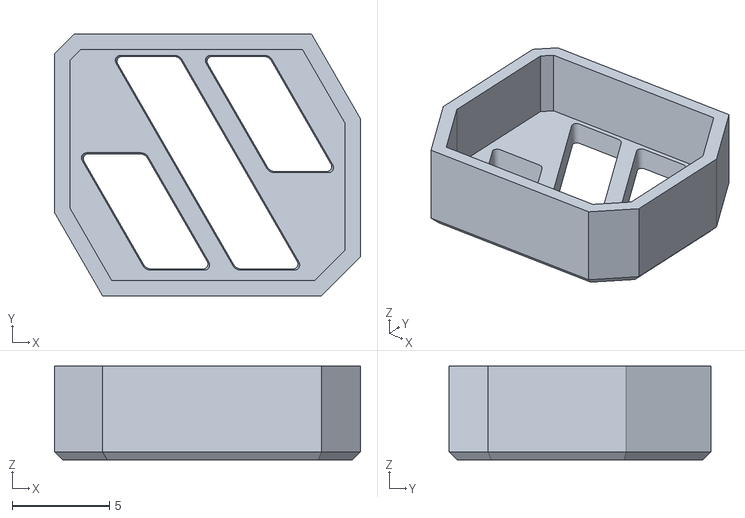
[picture p77: CAD file, 2025-08-13]
STL/Stealthburner/Stealthburner/[o]_stealthburner_LED_diffuser_mask.stl
15.7 x 13.4 x 4.80
