Nolicx/Voron-Trident/STL/Tap/Tap_Front_r8.stl

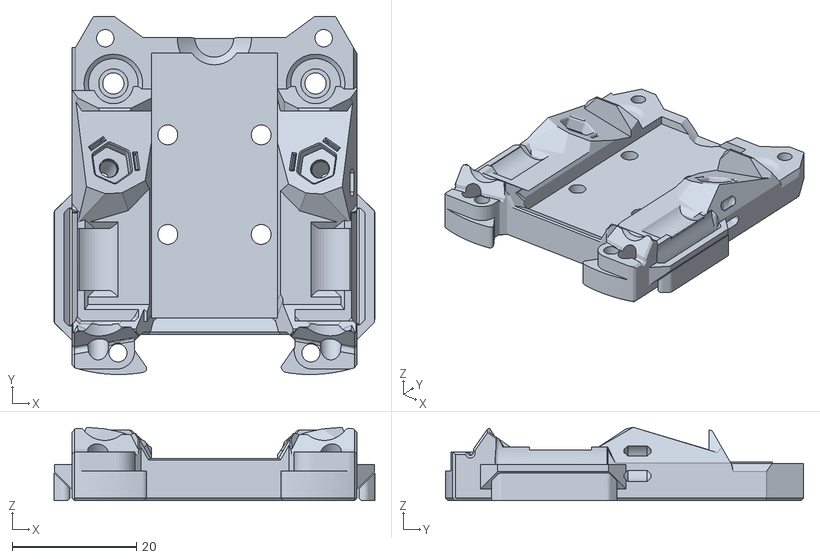
[picture p78: CAD file, 2025-08-13]
STL/Tap/Tap_Front_r8.stl
51.6 x 57.5 x 11.8
