Nolicx/Voron-Trident/STL/Tools/140mm_extrusion_drill_guide.stl

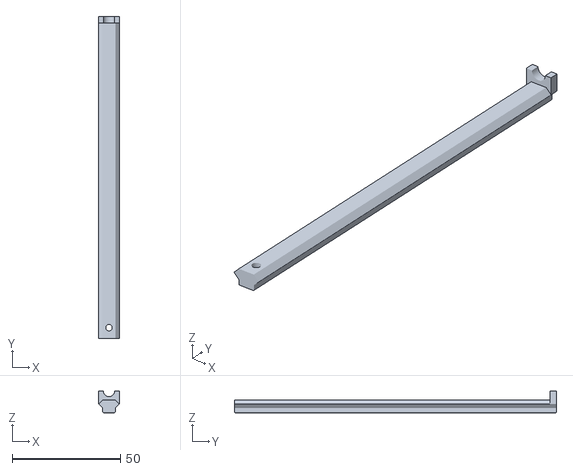
[picture p79: CAD file, 2025-08-13]
STL/Tools/140mm_extrusion_drill_guide.stl
9.60 x 148.8 x 10.1
