Nolicx/Voron-Trident/STL/Z_Assembly/[a]_z_rail_stop_x3.stl

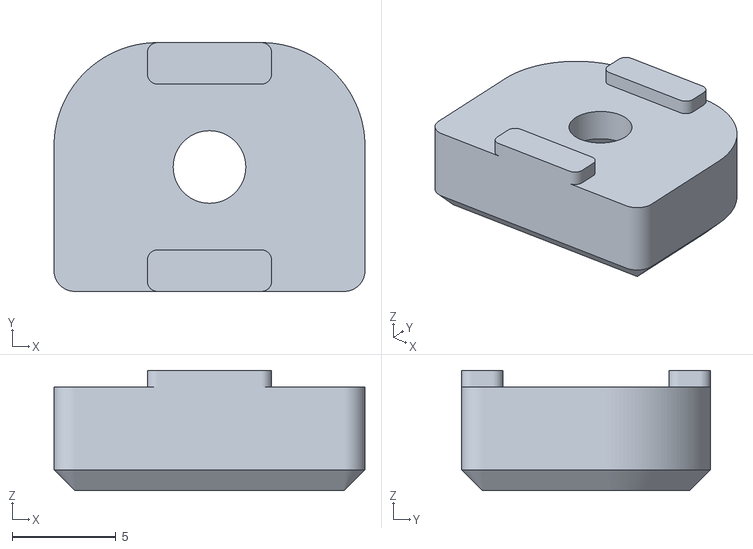
[picture p80: CAD file, 2025-08-13]
STL/Z_Assembly/[a]_z_rail_stop_x3.stl
15.0 x 12.0 x 5.80
