Nolicx/Voron-Trident/only custom STLs/Primary/Manta_M8P_2pc.stl

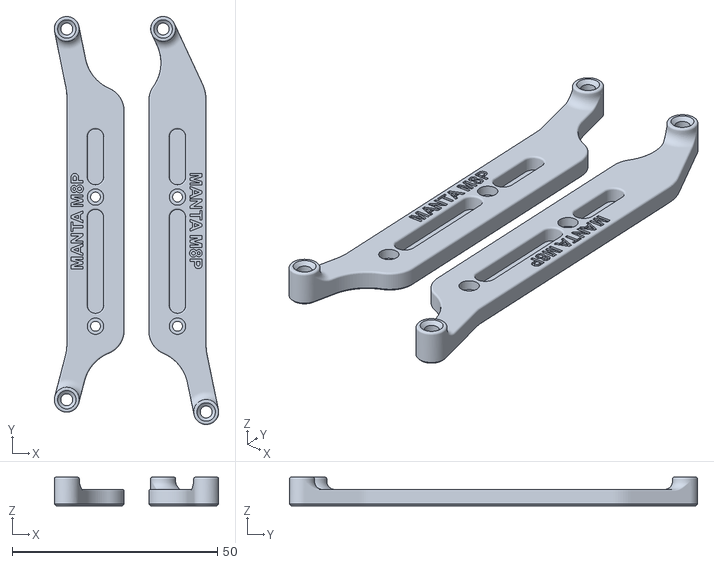
[picture p82: CAD file, 2025-08-13]
only custom STLs/Primary/Manta_M8P_2pc.stl
40.1 x 99.5 x 7.00
