Nolicx/Voron-Trident/STL/Gantry/AB_Drive_Units/b_drive_frame_upper.stl

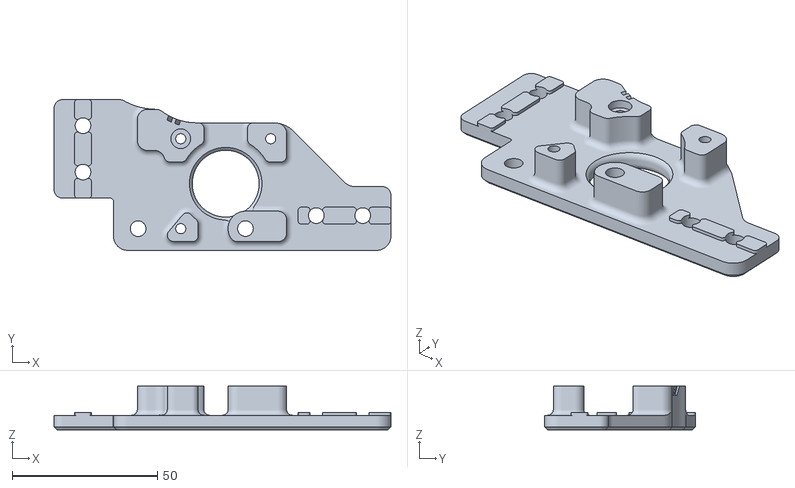
[picture p83: CAD file, 2025-08-13]
STL/Gantry/AB_Drive_Units/b_drive_frame_upper.stl
116.2 x 52.0 x 15.0
