Nolicx/Voron-Trident/STL/Gantry/Front_Idlers/front_idler_b_x2.stl

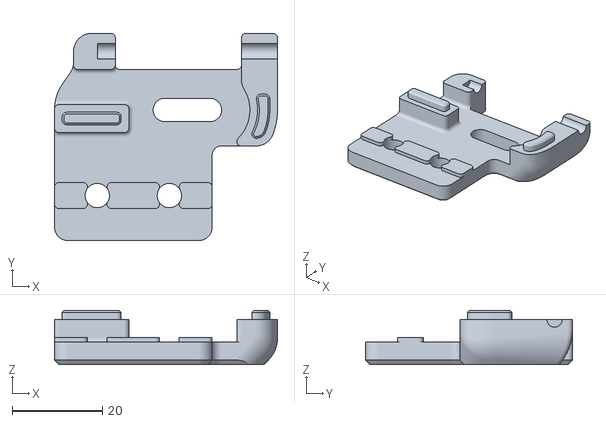
[picture p84: CAD file, 2025-08-13]
STL/Gantry/Front_Idlers/front_idler_b_x2.stl
49.5 x 46.0 x 12.0
