Nolicx/Voron-Trident/STL/Gantry/XY_Joints/[a]_xy_joint_cable_bridge_2hole.stl

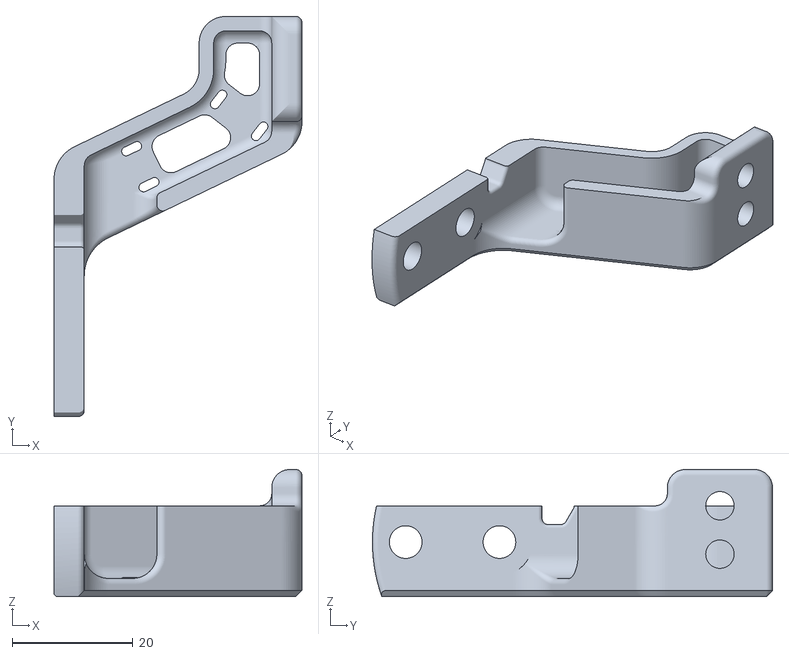
[picture p85: CAD file, 2025-08-13]
STL/Gantry/XY_Joints/[a]_xy_joint_cable_bridge_2hole.stl
41.0 x 66.1 x 21.0
