Nolicx/Voron-Trident/STL/Panels/Front_Doors/latch_x2.stl

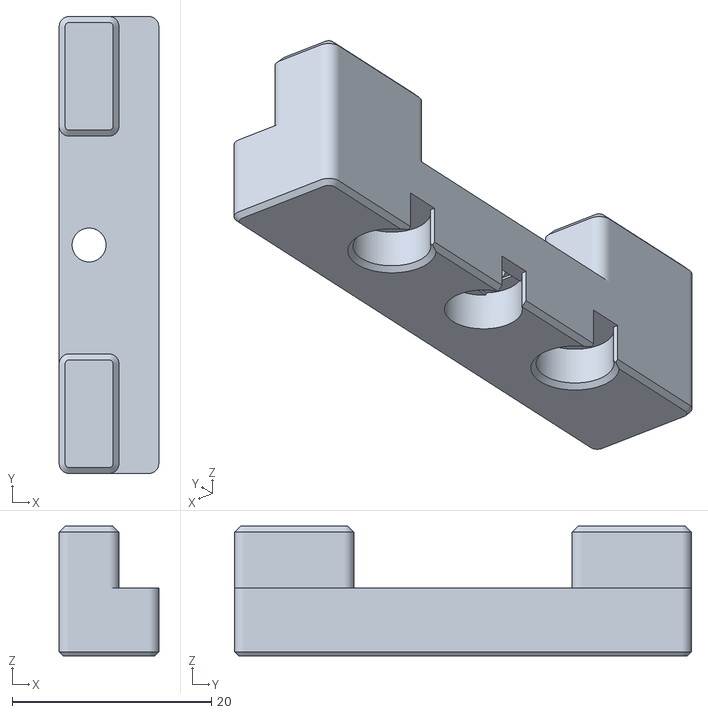
[picture p87: CAD file, 2025-08-13]
STL/Panels/Front_Doors/latch_x2.stl
10.0 x 45.9 x 13.0
