Nolicx/Voron-Trident/STL/Stealthburner/Clockwork2/Direct_Drive/motor_plate.stl

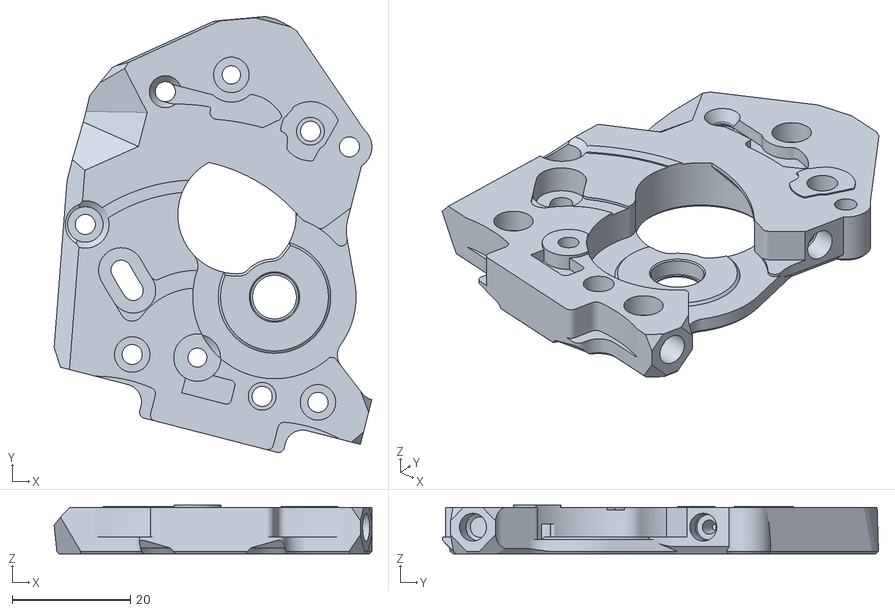
[picture p88: CAD file, 2025-08-13]
STL/Stealthburner/Clockwork2/Direct_Drive/motor_plate.stl
53.7 x 73.6 x 8.20
