Nolicx/Voron-Trident/STL/Stealthburner/Stealthburner/[c]_stealthburner_LED_diffuser.stl

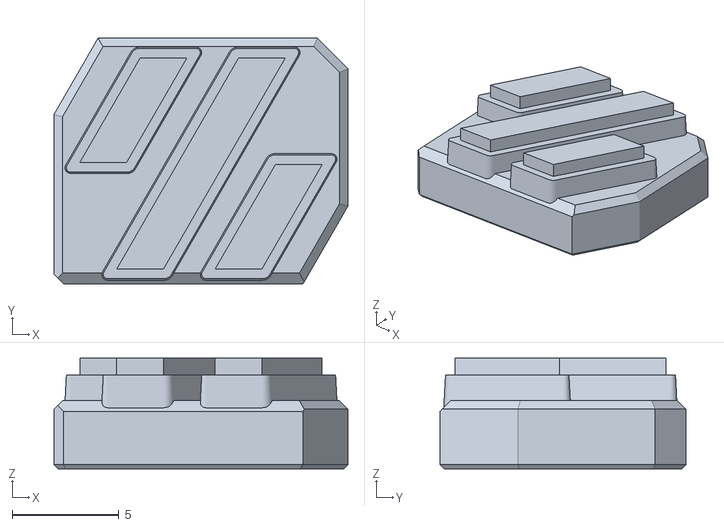
[picture p89: CAD file, 2025-08-13]
STL/Stealthburner/Stealthburner/[c]_stealthburner_LED_diffuser.stl
13.8 x 11.5 x 5.20
