Nolicx/Voron-Trident/STL/Tap/Tap_Center_left_r8.stl

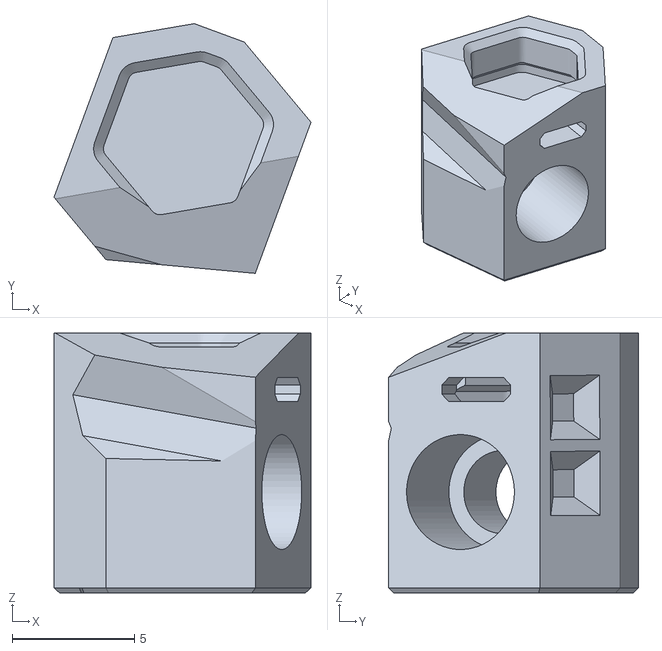
[picture p90: CAD file, 2025-08-13]
STL/Tap/Tap_Center_left_r8.stl
10.5 x 10.2 x 10.6
