Nolicx/Voron-Trident/STL/Tools/MGN9_rail_guide_x2.stl

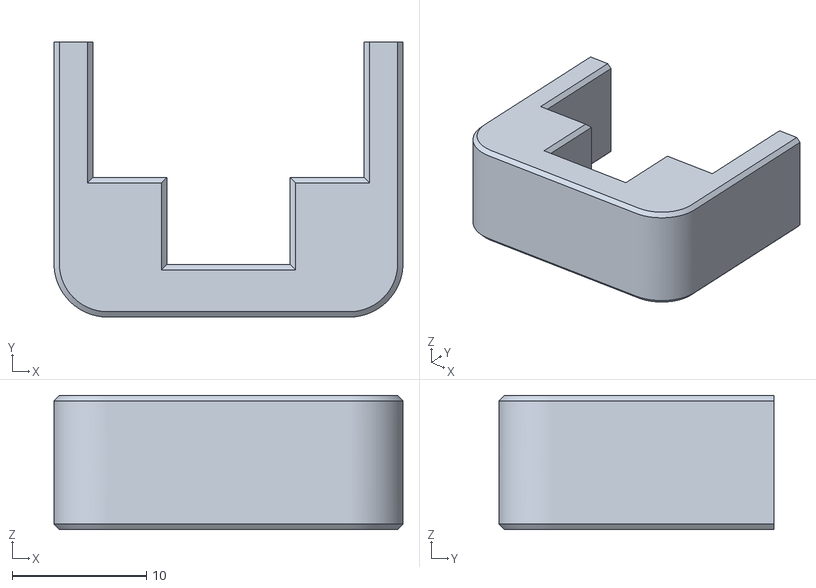
[picture p91: CAD file, 2025-08-13]
STL/Tools/MGN9_rail_guide_x2.stl
26.0 x 20.5 x 10.0
