Nolicx/Voron-Trident/STL/Z_Assembly/z_carriage_rear_3hole.stl

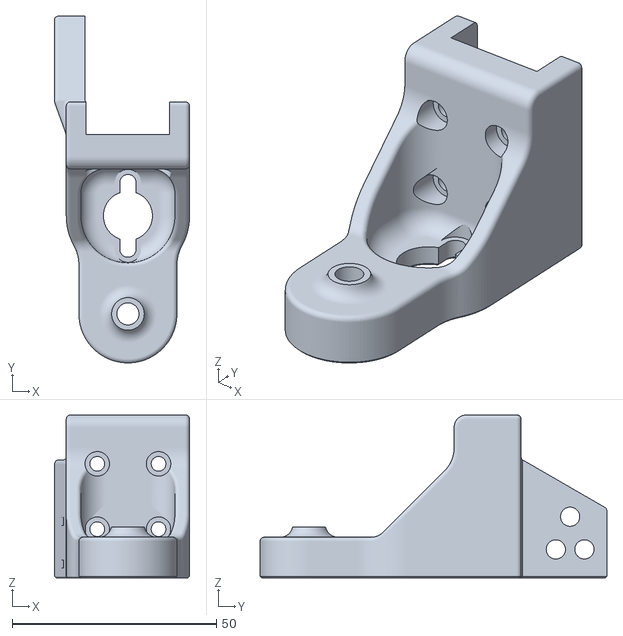
[picture p92: CAD file, 2025-08-13]
STL/Z_Assembly/z_carriage_rear_3hole.stl
33.1 x 84.9 x 39.9
