Nolicx/Voron-Trident/Mods/ptfe_bowden_guide/voron-bowden-ptfe-tube-guide-arm-and-canbus-cable-support-model_files/STL's/mount.stl

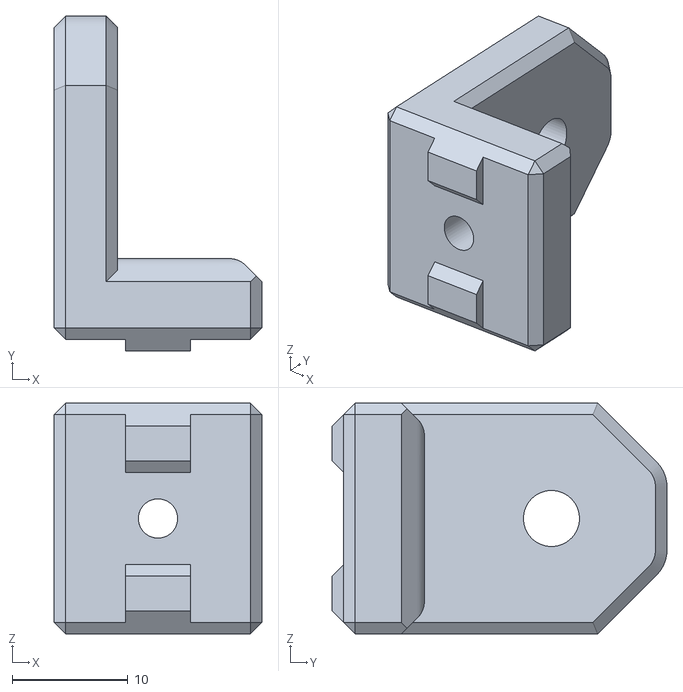
[picture p93: CAD file, 2026-05-21]
Mods/ptfe_bowden_guide/voron-bowden-ptfe-tube-guide-arm-and-canbus-cable-support-model_files/STL's/mount.stl
18.0 x 29.0 x 20.0
