Nolicx/Voron-Trident/only custom STLs/Primary/3-6.STL

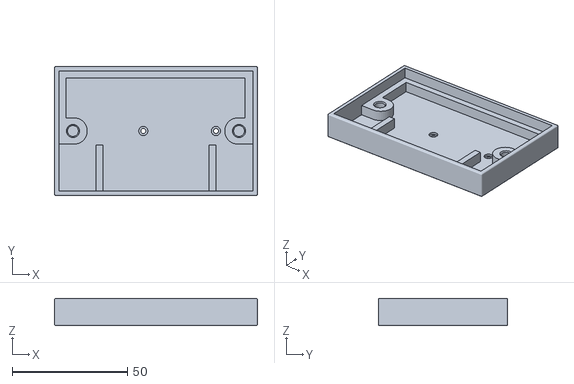
[picture p94: CAD file, 2025-08-13]
only custom STLs/Primary/3-6.STL
88.0 x 56.0 x 11.8
