Nolicx/Voron-Trident/STL/Exhaust_Filter/[a]_exhaust_filter_mount_x2.stl

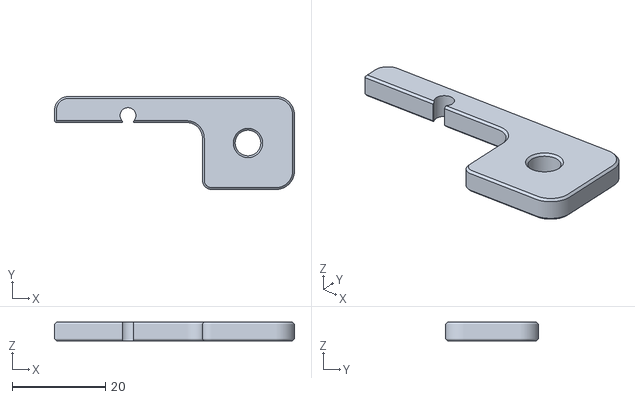
[picture p95: CAD file, 2025-08-13]
STL/Exhaust_Filter/[a]_exhaust_filter_mount_x2.stl
51.6 x 20.0 x 4.00
