Nolicx/Voron-Trident/STL/Gantry/XY_Joints/xy_joint_right_upper_MGN12.stl

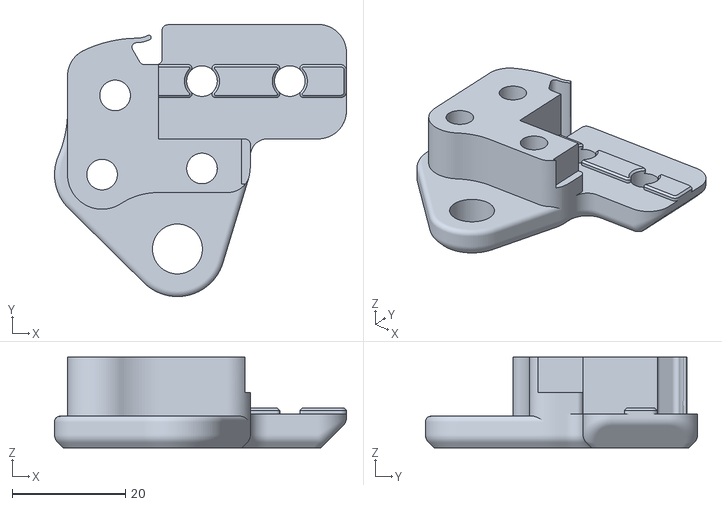
[picture p96: CAD file, 2025-08-13]
STL/Gantry/XY_Joints/xy_joint_right_upper_MGN12.stl
51.5 x 48.0 x 16.0
