Nolicx/Voron-Trident/STL/Panels/corner_panel_clip_4mm_x8.stl

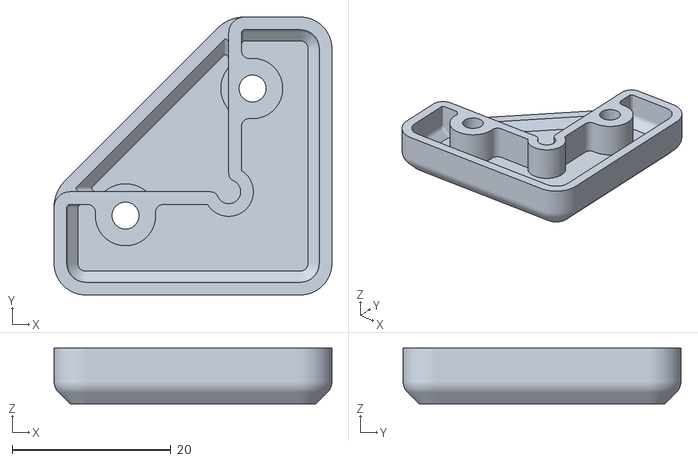
[picture p97: CAD file, 2025-08-13]
STL/Panels/corner_panel_clip_4mm_x8.stl
35.0 x 35.0 x 7.00
