Nolicx/Voron-Trident/STL/Skirt/250/rear_center_skirt_250.stl

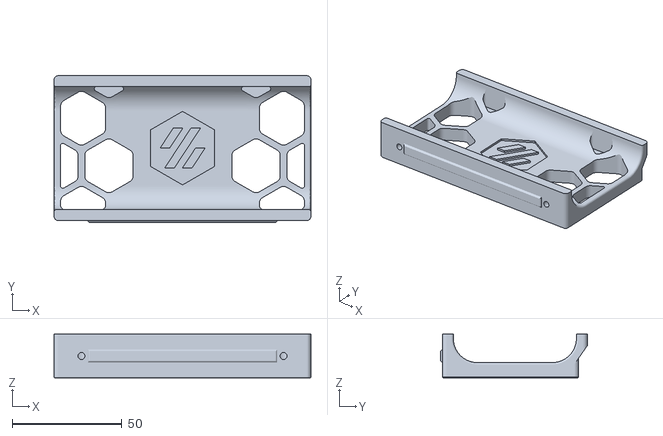
[picture p98: CAD file, 2025-08-13]
STL/Skirt/250/rear_center_skirt_250.stl
117.0 x 66.8 x 20.0
