Nolicx/Voron-Trident/STL/Skirt/350/rear_center_skirt_350.stl

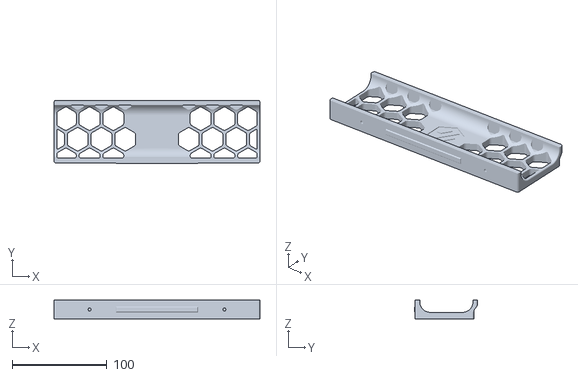
[picture p99: CAD file, 2025-08-13]
STL/Skirt/350/rear_center_skirt_350.stl
217.0 x 66.8 x 20.0
