Nolicx/Voron-Trident/STL/Skirt/[a]_corner_baseplate_a_x2.stl

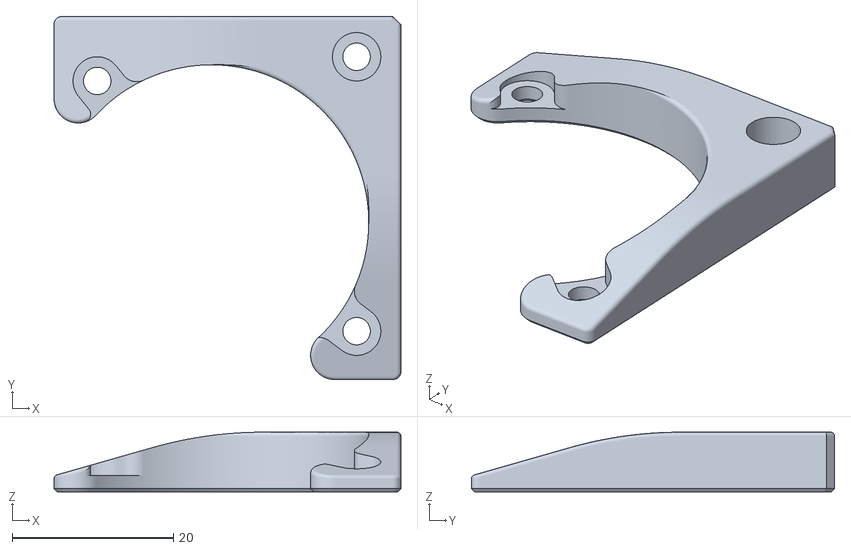
[picture p100: CAD file, 2025-08-13]
STL/Skirt/[a]_corner_baseplate_a_x2.stl
43.0 x 45.0 x 7.40
