Nolicx/Voron-Trident/STL/Stealthburner/Clockwork2/Direct_Drive/[a]_guidler_a.stl

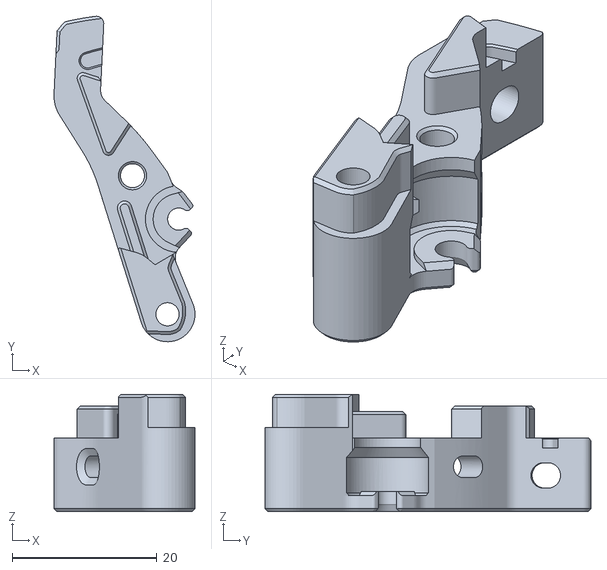
[picture p101: CAD file, 2025-08-13]
STL/Stealthburner/Clockwork2/Direct_Drive/[a]_guidler_a.stl
19.5 x 45.0 x 16.2
