Nolicx/Voron-Trident/STL/Tap/Tap_Center_right_r8.stl

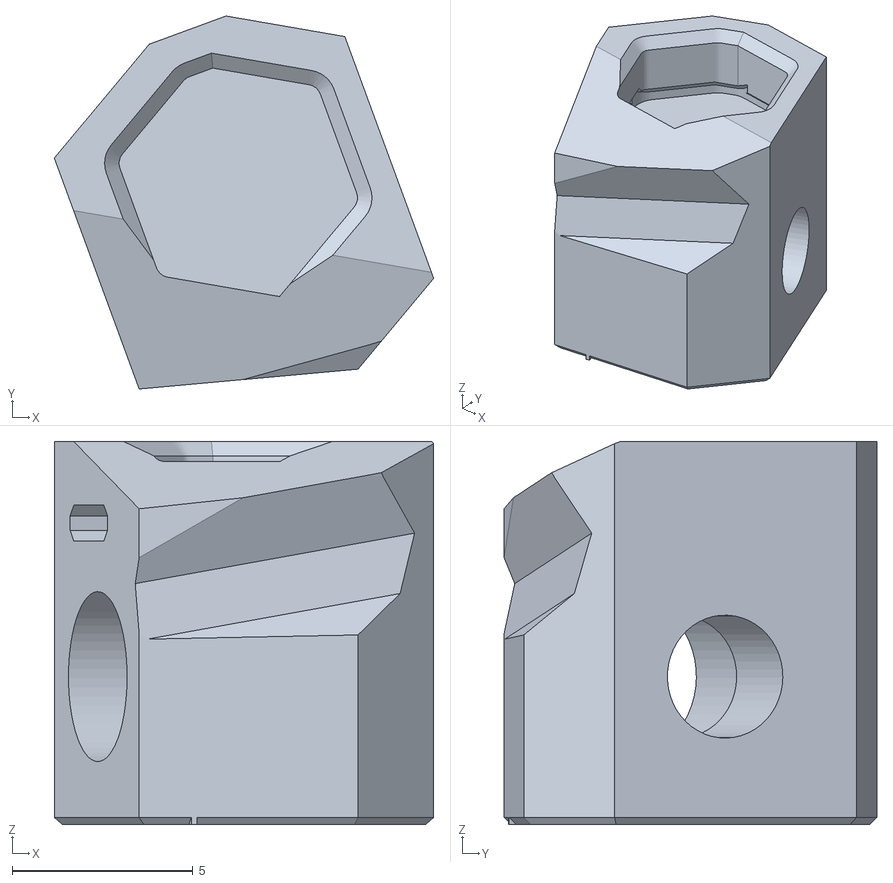
[picture p102: CAD file, 2025-08-13]
STL/Tap/Tap_Center_right_r8.stl
10.5 x 10.3 x 10.6
