Nolicx/Voron-Trident/STL/Tools/10mm_extrusion_drill_guide.stl

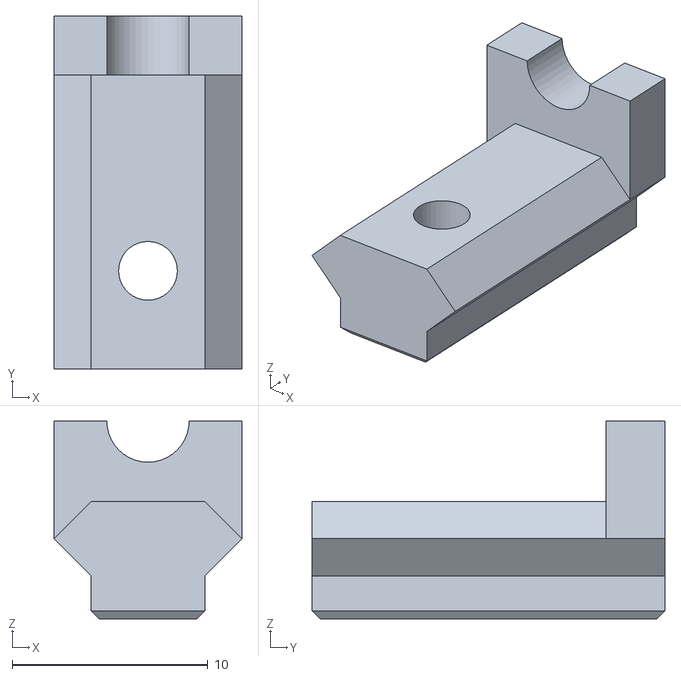
[picture p103: CAD file, 2025-08-13]
STL/Tools/10mm_extrusion_drill_guide.stl
9.60 x 18.0 x 10.1
