Nolicx/Voron-Trident/STL/Z_Assembly/z_carriage_right.stl

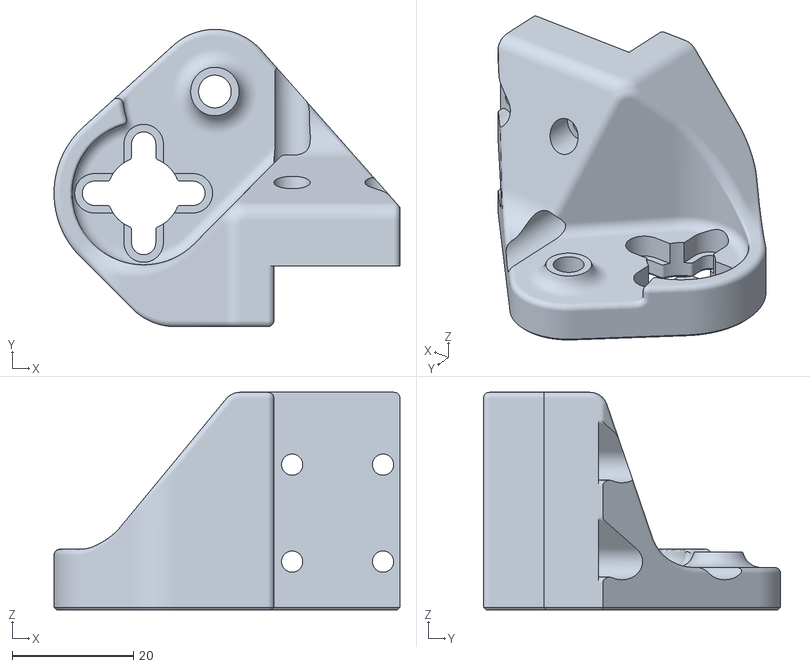
[picture p104: CAD file, 2025-08-13]
STL/Z_Assembly/z_carriage_right.stl
57.1 x 49.1 x 35.9
