Nolicx/Voron-Trident/STL/ElectronicsBay/PSU_stabilizer_50mm.stl

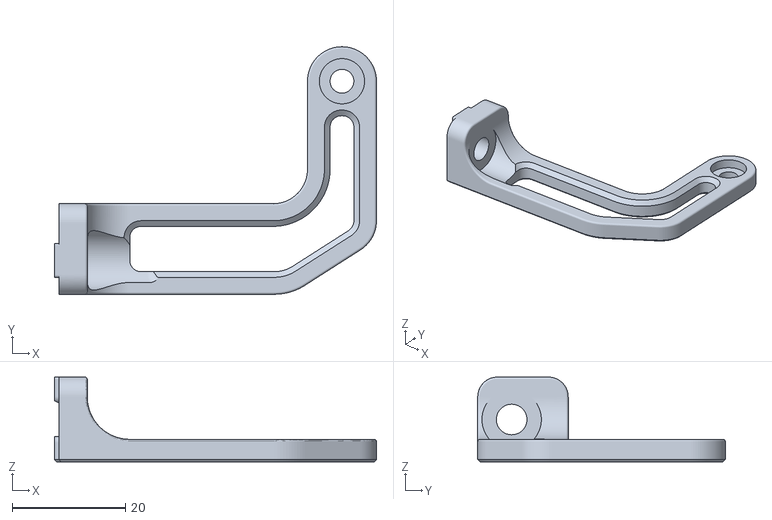
[picture p105: CAD file, 2025-08-13]
STL/ElectronicsBay/PSU_stabilizer_50mm.stl
56.9 x 43.8 x 15.0
