Nolicx/Voron-Trident/STL/Gantry/XY_Joints/xy_joint_right_lower_MGN12.stl

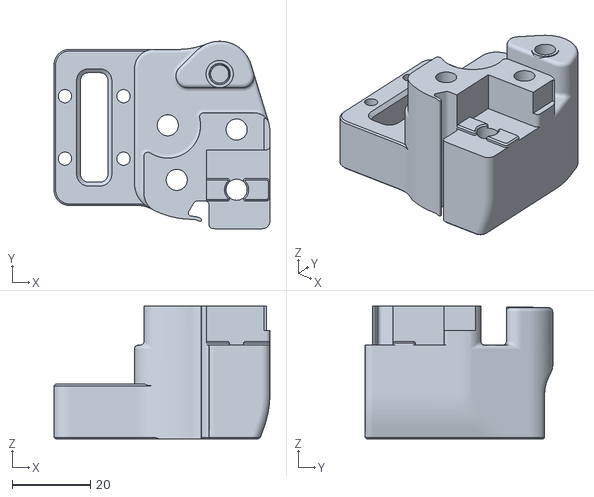
[picture p107: CAD file, 2025-08-13]
STL/Gantry/XY_Joints/xy_joint_right_lower_MGN12.stl
55.3 x 48.0 x 34.0
