Nolicx/Voron-Trident/STL/Panels/midspan_panel_clip_6mm_x8.stl

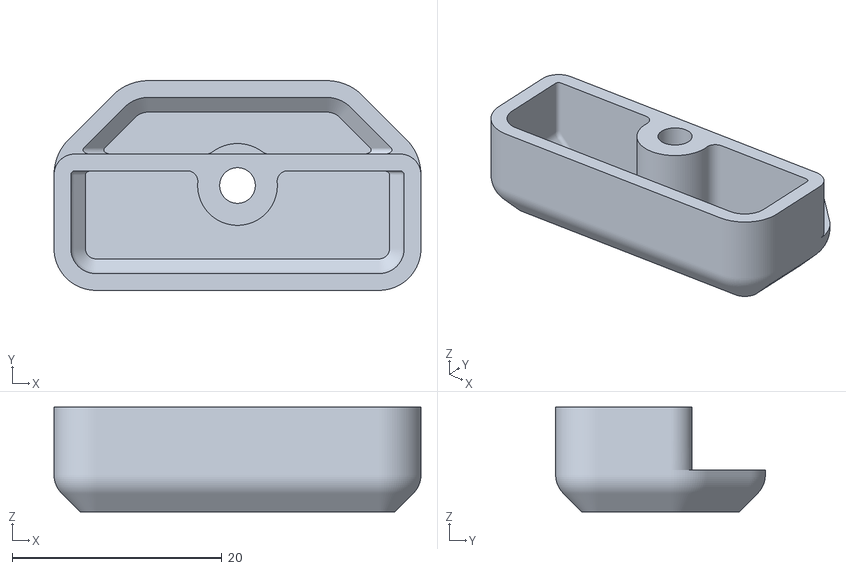
[picture p108: CAD file, 2025-08-13]
STL/Panels/midspan_panel_clip_6mm_x8.stl
35.0 x 20.0 x 10.00
