Nolicx/Voron-Trident/STL/Stealthburner/Clockwork2/Direct_Drive/[a]_latch.stl

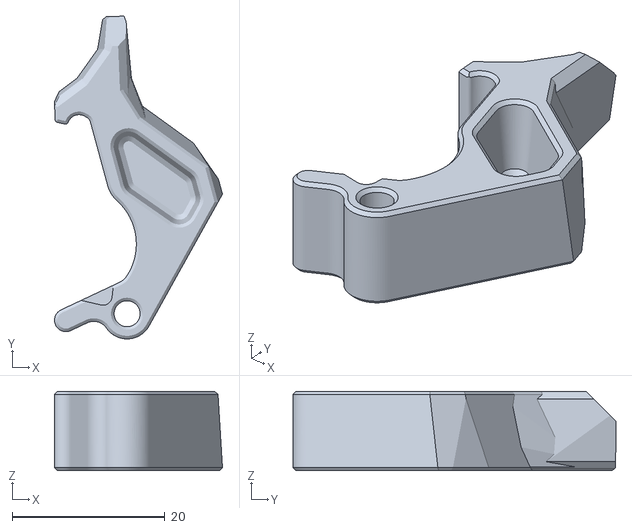
[picture p109: CAD file, 2025-08-13]
STL/Stealthburner/Clockwork2/Direct_Drive/[a]_latch.stl
22.0 x 42.3 x 10.4
