Nolicx/Voron-Trident/STL/Tools/110mm_Y_alignment_spacer_x2.stl

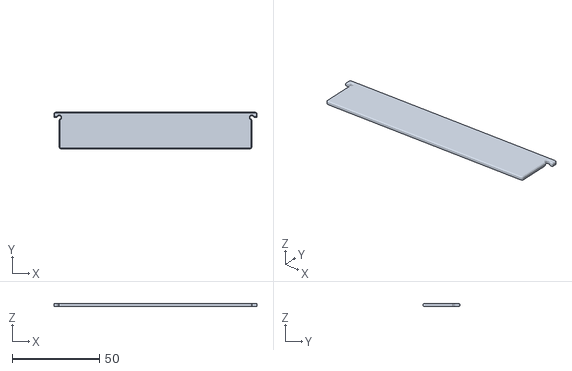
[picture p110: CAD file, 2025-08-13]
STL/Tools/110mm_Y_alignment_spacer_x2.stl
116.5 x 21.0 x 2.00
