Nolicx/Voron-Trident/Mods/ptfe_bowden_guide/voron-bowden-ptfe-tube-guide-arm-and-canbus-cable-support-model_files/STL's/under_extrusion_mount_bearing.stl

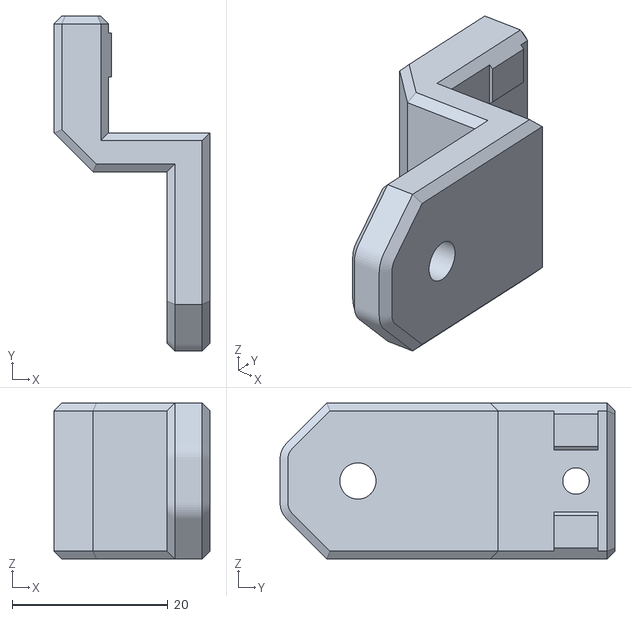
[picture p111: CAD file, 2026-05-21]
Mods/ptfe_bowden_guide/voron-bowden-ptfe-tube-guide-arm-and-canbus-cable-support-model_files/STL's/under_extrusion_mount_bearing.stl
20.0 x 43.0 x 20.0
