Nolicx/Voron-Trident/STL/ElectronicsBay/DIN_center_support_x2.stl

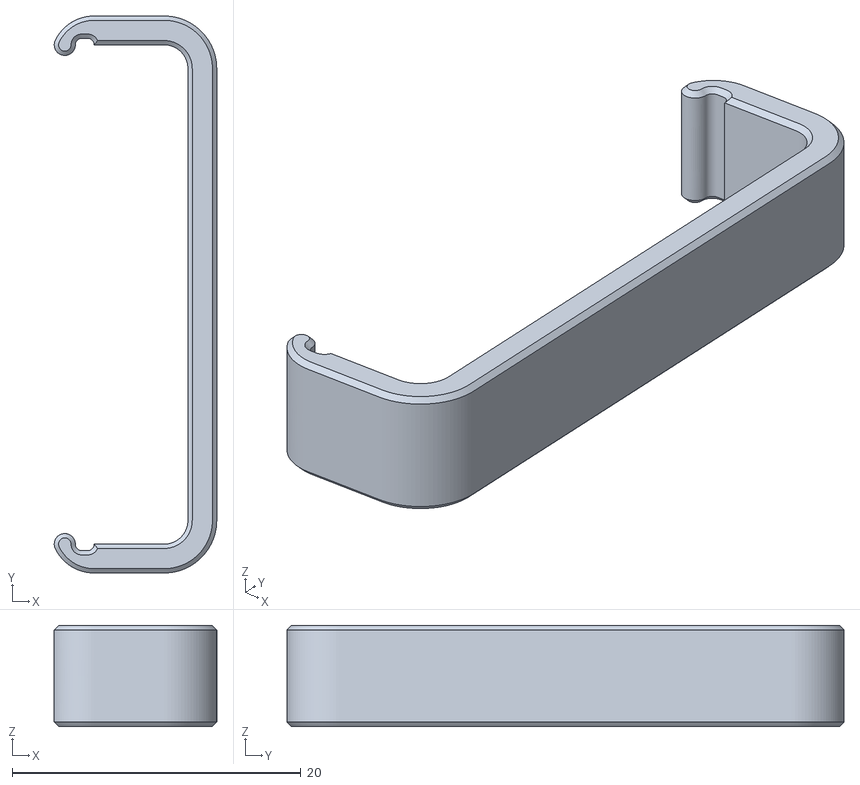
[picture p112: CAD file, 2025-08-13]
STL/ElectronicsBay/DIN_center_support_x2.stl
11.3 x 38.6 x 7.00
