Nolicx/Voron-Trident/STL/Gantry/AB_Drive_Units/a_drive_frame_lower.stl

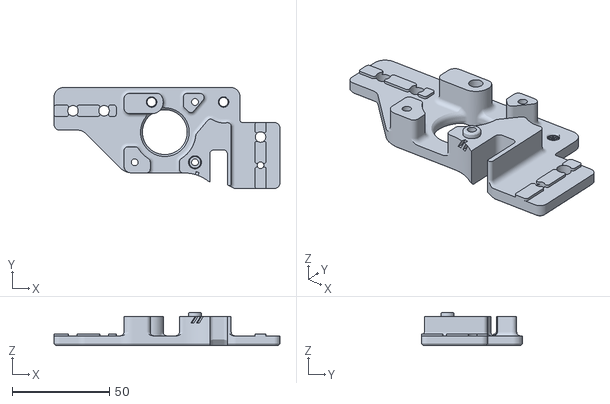
[picture p113: CAD file, 2025-08-13]
STL/Gantry/AB_Drive_Units/a_drive_frame_lower.stl
116.2 x 52.0 x 17.0
