Nolicx/Voron-Trident/STL/Gantry/XY_Joints/[a]_xy_joint_cable_bridge_3hole.stl

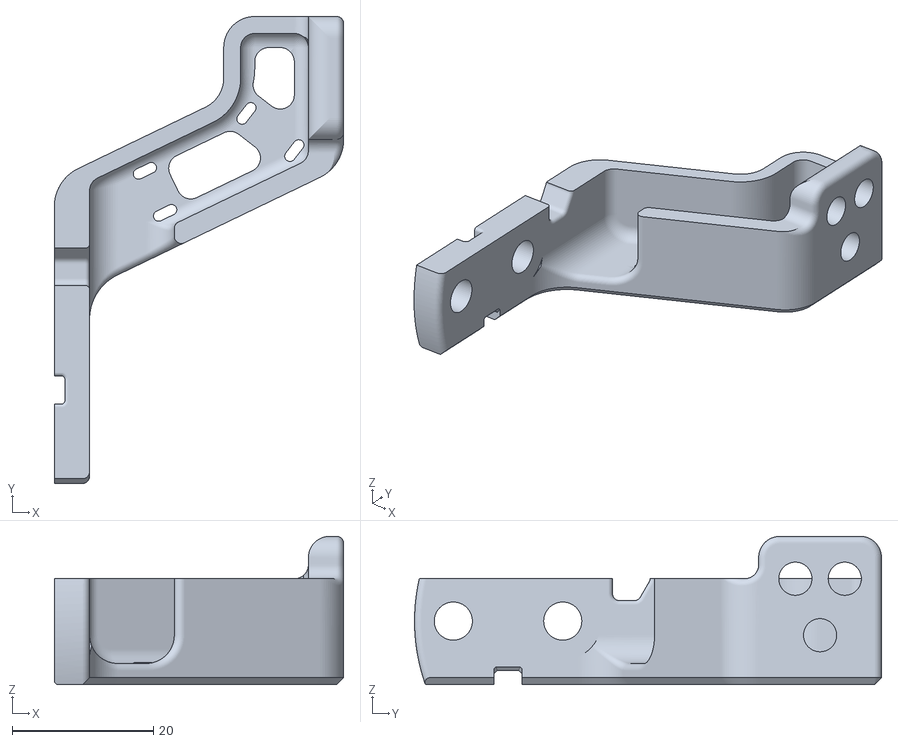
[picture p114: CAD file, 2025-08-13]
STL/Gantry/XY_Joints/[a]_xy_joint_cable_bridge_3hole.stl
41.0 x 66.1 x 21.0
