Nolicx/Voron-Trident/STL/Panels/midspan_panel_clip_4mm_x7.stl

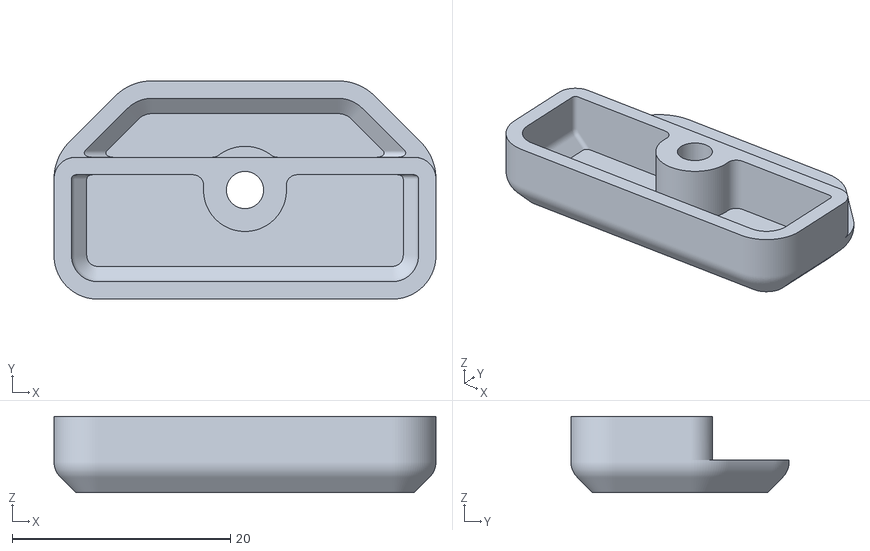
[picture p115: CAD file, 2025-08-13]
STL/Panels/midspan_panel_clip_4mm_x7.stl
35.0 x 20.0 x 7.00
