Nolicx/Voron-Trident/STL/Skirt/corner_a_x2.stl

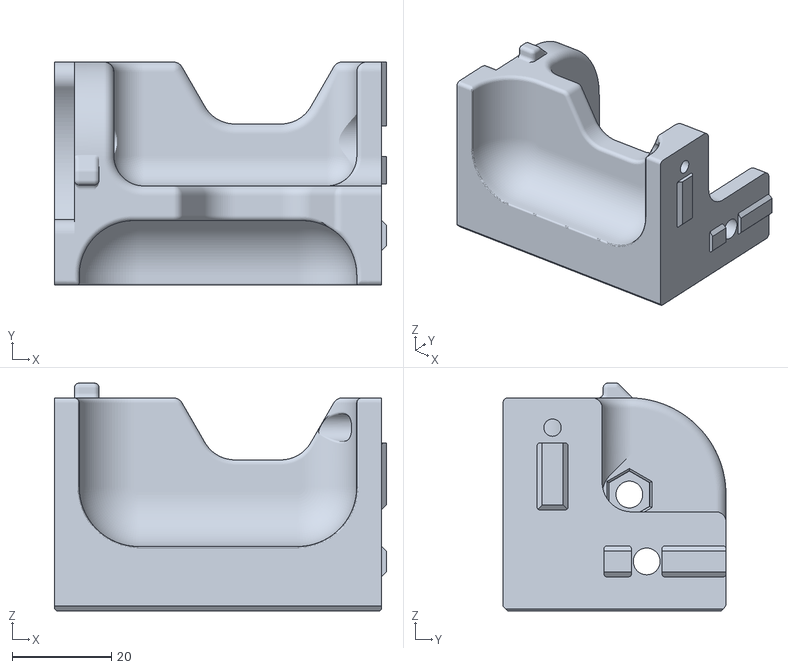
[picture p116: CAD file, 2025-08-13]
STL/Skirt/corner_a_x2.stl
67.0 x 45.0 x 46.0
