Nolicx/Voron-Trident/STL/Z_Assembly/[a]_z_carriage_left.stl

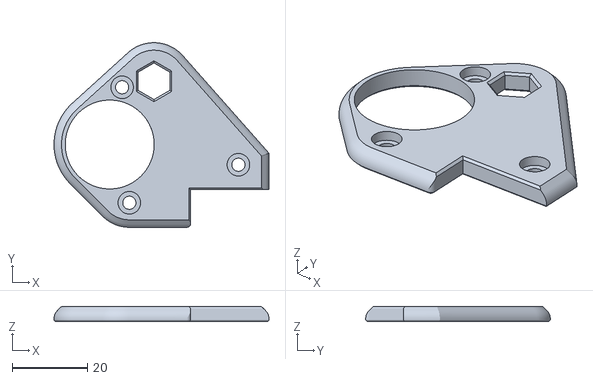
[picture p117: CAD file, 2025-08-13]
STL/Z_Assembly/[a]_z_carriage_left.stl
57.1 x 49.0 x 4.00
