Nolicx/Voron-Trident/STL/Panels/bottom_panel_clip_x4.stl

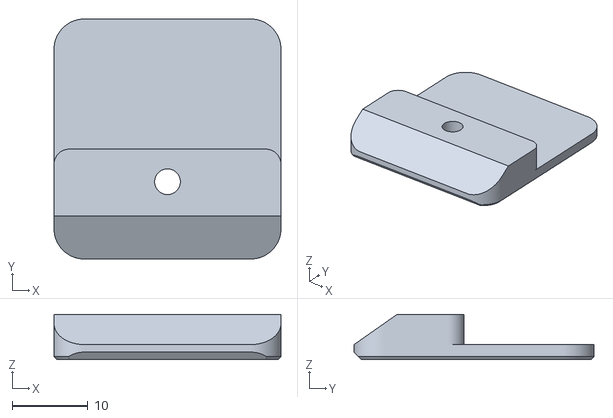
[picture p120: CAD file, 2025-08-13]
STL/Panels/bottom_panel_clip_x4.stl
30.0 x 31.7 x 6.00
