Nolicx/Voron-Trident/STL/Skirt/[a]_skirt_logo_x2.stl

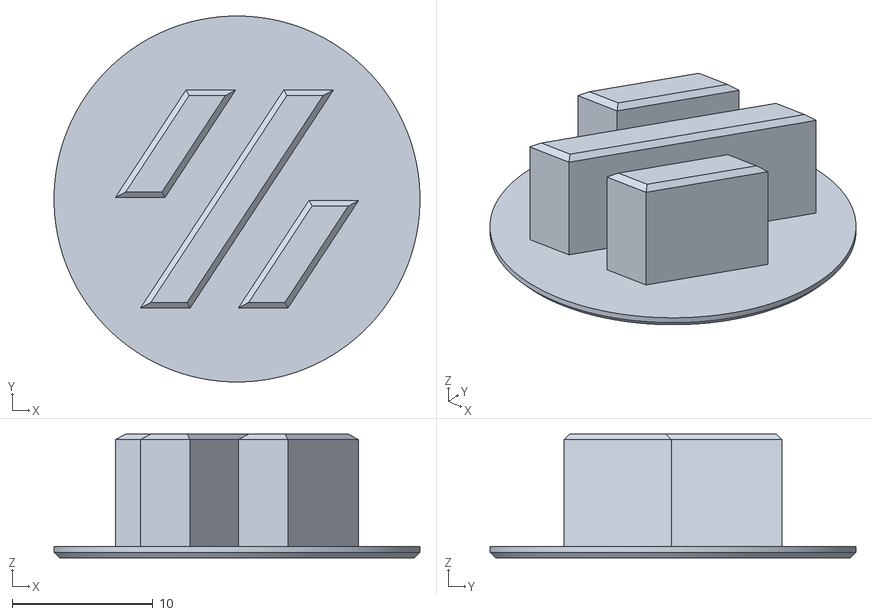
[picture p122: CAD file, 2025-08-13]
STL/Skirt/[a]_skirt_logo_x2.stl
26.0 x 26.0 x 8.80
