Nolicx/Voron-Trident/STL/Z_Assembly/z_stepper_rear.stl

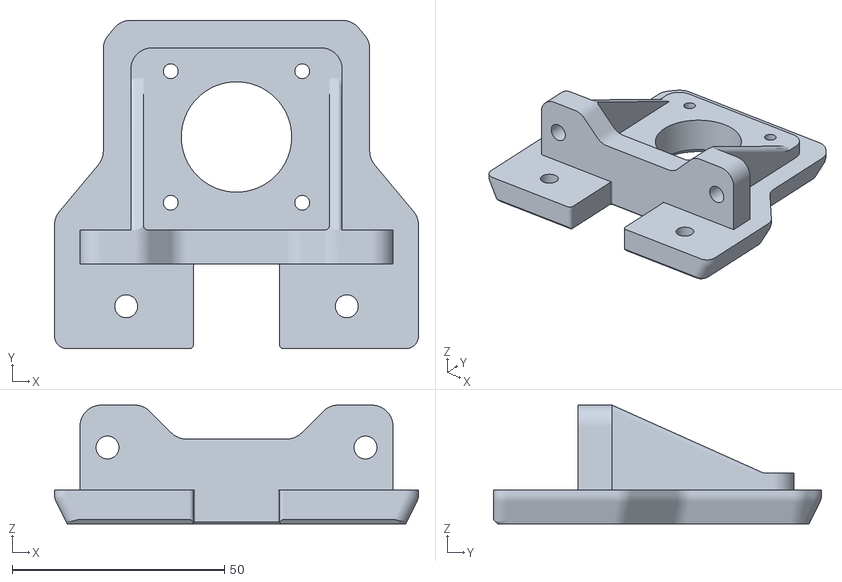
[picture p123: CAD file, 2025-08-13]
STL/Z_Assembly/z_stepper_rear.stl
85.8 x 77.4 x 28.0
